ChrisM90/TeensyBoy/Arduino/TeensyBoy/GBA.cpp

/* TeenyBoy code is placed under the MIT license
   Copyright (c) 2017 Chris Mortimer

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
   THE SOFTWARE IS PROVIDED "AS IS", WITHOUT WARRANTY OF ANY KIND,
   EXPRESS OR IMPLIED, INCLUDING BUT NOT LIMITED TO THE WARRANTIES OF
   MERCHANTABILITY, FITNESS FOR A PARTICULAR PURPOSE AND
   NONINFRINGEMENT. IN NO EVENT SHALL THE AUTHORS OR COPYRIGHT HOLDERS
   BE LIABLE FOR ANY CLAIM, DAMAGES OR OTHER LIABILITY, WHETHER IN AN
   ACTION OF CONTRACT, TORT OR OTHERWISE, ARISING FROM, OUT OF OR IN
   CONNECTION WITH THE SOFTWARE OR THE USE OR OTHER DEALINGS IN THE
   SOFTWARE.
*/

#include "GBA.h"

#define SCREEN_WIDTH  ILI9341_TFTWIDTH
#define SCREEN_HEIGHT ILI9341_TFTHEIGHT
#define TFT_DC      15
#define TFT_CS      10
#define TFT_RST     27
#define TFT_MOSI    11
#define TFT_SCLK    13
#define TFT_MISO    12

#define WIN0H 0x40
#define WIN1H 0x42
#define WIN0V 0x44
#define WIN1V 0x46
#define WININ 0x48
#define WINOUT 0x4A

#define BG0CNT 0x8
#define BG1CNT 0xA
#define BG2CNT 0xC
#define BG3CNT 0xE

#define BG2X_L 0x28
#define BG2X_H 0x2A
#define BG2Y_L 0x2C
#define BG2Y_H 0x2E

#define BG3X_L 0x38
#define BG3X_H 0x3A
#define BG3Y_L 0x3C
#define BG3Y_H 0x3E

#define DISPCNT 0x0
#define DISPSTAT 0x4

#define ioRegStart  0x00048000 //0x48000 - 0x484FF = 0x4FF
#define vRamStart   0x00048500 //0x48500 - 0x684FF = 0x1FFFF
#define palRamStart 0x00068500 //0x68500 - 0x688FF = 0x3FF
#define OAM_BASE 0x7000000

#define ButtonA 18
#define ButtonB 17
#define ButtonSelect 26
#define ButtonStart 16
#define ButtonLeft 20
#define ButtonRight 19
#define ButtonUp 22
#define ButtonDown 21
#define ButtonRSholder 38
#define ButtonLSholder 39

int32_t vramCycles = 0;
bool inHblank = false;
uint16_t curLine = 0;

// Window helper variables
uint8_t win0x1, win0x2, win0y1, win0y2;
uint8_t win1x1, win1x2, win1y1, win1y2;
uint8_t win0Enabled, win1Enabled, winObjEnabled, winOutEnabled;
bool winEnabled;

uint8_t blendSource, blendTarget;
uint8_t blendA, blendB, blendY;
int32_t blendType;
uint16_t dispCnt;

uint8_t windowCover[240];
uint8_t Blend[240];

unsigned long FrameTime = 0;

Processor *processor;

void GBA::Initilise(class File *rom)
{  
  ILI9341_t3DMA screen = ILI9341_t3DMA(TFT_CS, TFT_DC, TFT_RST, TFT_MOSI, TFT_SCLK, TFT_MISO);
  tft = &screen;
  tft->begin();
  tft->dfillScreen(ILI9341_BLACK);
  tft->refreshOnce();

  pinMode(ButtonA, INPUT_PULLUP);
  pinMode(ButtonB, INPUT_PULLUP);
  pinMode(ButtonSelect, INPUT_PULLUP);
  pinMode(ButtonStart, INPUT_PULLUP);
  pinMode(ButtonLeft, INPUT_PULLUP);
  pinMode(ButtonRight, INPUT_PULLUP);
  pinMode(ButtonUp, INPUT_PULLUP);
  pinMode(ButtonDown, INPUT_PULLUP);
  pinMode(ButtonRSholder, INPUT_PULLUP);
  pinMode(ButtonLSholder, INPUT_PULLUP);

  Processor GBAProcessor;
  processor = &GBAProcessor;
  processor->CreateCores(processor, rom, false);
}

void GBA::Update()
{
  const int32_t numSteps = 2284;
  const int32_t cycleStep = 123;
  
  for (int32_t i = 0; i < numSteps; i++)
  {
    GetButtons();
    
    if (vramCycles <= 0)
    {
      if (inHblank)
      {
        vramCycles += 960;
        LeaveHBlank();
        inHblank = false;
      }
      else
      {
        vramCycles += 272;
        RenderLine();
        EnterHBlank();
        inHblank = true;
      }
    }

    processor->Execute(cycleStep);

    vramCycles -= cycleStep;

    processor->FireIrq();
  }
}

void GBA::EnterVBlank()
{
  uint16_t dispstat = processor->ReadU16(DISPSTAT, ioRegStart); //Read DISPSTAT 0x4 from IOReg
  dispstat |= 1;
  processor->WriteU16(DISPSTAT, ioRegStart, dispstat);//Write new DISPSTAT 0x4 to IOReg

  // Render the frame

  if(FrameTime != 0)
  {
    FPS = 1000000.0f / (float)(micros() - FrameTime);
  }

  Serial.println("FPS: " + String(FPS));
  tft->refreshOnce();
  FrameTime = micros();
  
  if ((dispstat & (1 << 3)) != 0)
  {
    // Fire the vblank irq
    processor->RequestIrq(0);
  }

  // Check for DMA triggers
  processor->VBlankDma();
}

void GBA::LeaveVBlank()
{
  uint16_t dispstat = processor->ReadU16(DISPSTAT, ioRegStart); //Read DISPSTAT 0x4 from IOReg
  dispstat &= 0xFFFE;
  processor->WriteU16(DISPSTAT, ioRegStart, dispstat);//Write new DISPSTAT 0x4 to IOReg

  processor->UpdateKeyState();

  // Update the rot/scale values
  processor->bgx[0] = (int32_t)processor->ReadU32(BG2X_L, ioRegStart); //Read BG2X_L from IOReg
  processor->bgx[1] = (int32_t)processor->ReadU32(BG3X_L, ioRegStart); //Read BG3X_L from IOReg
  processor->bgy[0] = (int32_t)processor->ReadU32(BG2Y_L, ioRegStart); //Read BG2Y_L from IOReg
  processor->bgy[1] = (int32_t)processor->ReadU32(BG3Y_L, ioRegStart); //Read BG3Y_L from IOReg
}

void GBA::EnterHBlank()
{
  uint16_t dispstat = processor->ReadU16(DISPSTAT, ioRegStart); //Read DISPSTAT 0x4 from IOReg
  dispstat |= 1 << 1;
  processor->WriteU16(DISPSTAT, ioRegStart, dispstat);//Write new DISPSTAT 0x4 to IOReg

  // Advance the bgx registers
  for (int32_t bg = 0; bg <= 1; bg++)
  {
    int16_t dmx = (int16_t)processor->ReadU16(BG2PB + (uint32_t)bg * 0x10, ioRegStart); //Read BG2PB from IOReg
    int16_t dmy = (int16_t)processor->ReadU16(BG2PD+ (uint32_t)bg * 0x10, ioRegStart); //Read BG2PD from IOReg
    processor->bgx[bg] += dmx;
    processor->bgy[bg] += dmy;
  }

  if (curLine < 160)
  {
    processor->HBlankDma();

    // Trigger hblank irq
    if ((dispstat & (1 << 4)) != 0)
    {
      processor->RequestIrq(1);
    }
  }
}

void GBA::LeaveHBlank()
{
  uint16_t dispstat = processor->ReadU16(DISPSTAT, ioRegStart); //Read DISPSTAT 0x4 from IOReg
  dispstat &= 0xFFF9;
  processor->WriteU16(DISPSTAT, ioRegStart, dispstat);//Write new DISPSTAT 0x4 to IOReg

  // Move to the next line
  curLine++;

  if (curLine >= 228)
  {
    // Start again at the beginning
    curLine = 0;
  }

  // Update registers
  processor->WriteU16(VCOUNT, ioRegStart, (uint16_t)curLine); //Write VCOUNT 0x6 in IOReg

  // Check for vblank
  if (curLine == 160)
  {
    EnterVBlank();
  }
  else if (curLine == 0)
  {
    LeaveVBlank();
  }

  // Check y-line trigger
  if (((dispstat >> 8) & 0xff) == curLine)
  {
    dispstat = (uint16_t)(processor->ReadU16(DISPSTAT, ioRegStart) | (1 << 2)); //Read DISPSTAT 0x4 from IOReg
    processor->WriteU16(DISPSTAT, ioRegStart, dispstat);//Write new DISPSTAT 0x4 to IOReg

    if ((dispstat & (1 << 5)) != 0)
    {
      processor->RequestIrq(2);
    }
  }
}

void GBA::GetButtons()
{
  //Button Index
  // 0 = A
  // 1 = B
  // 2 = Select
  // 3 = Start
  // 4 = Right
  // 5 = Left
  // 6 = Up
  // 7 = Down
  // 8 = Right Sholder
  // 9 = Left Sholder
  
  uint16_t keyreg = 0x3FF;

  if(!digitalReadFast(ButtonA))
  {
    keyreg &= (uint16_t)(~(1U << 0)); //Pressed
  }
  else
  {
    keyreg |= (uint16_t)(1U << 0); //Unpressed
  }

  if(!digitalReadFast(ButtonB))
  {
    keyreg &= (uint16_t)(~(1U << 1)); //Pressed
  }
  else
  {
    keyreg |= (uint16_t)(1U << 1); //Unpressed
  }

  if(!digitalReadFast(ButtonSelect))
  {
    keyreg &= (uint16_t)(~(1U << 2)); //Pressed
  }
  else
  {
    keyreg |= (uint16_t)(1U << 2); //Unpressed
  }

  if(!digitalReadFast(ButtonStart))
  {
    keyreg &= (uint16_t)(~(1U << 3)); //Pressed
  }
  else
  {
    keyreg |= (uint16_t)(1U << 3); //Unpressed
  }

  if(!digitalReadFast(ButtonLeft))
  {
    keyreg &= (uint16_t)(~(1U << 4)); //Pressed
  }
  else
  {
    keyreg |= (uint16_t)(1U << 4); //Unpressed
  }

  if(!digitalReadFast(ButtonRight))
  {
    keyreg &= (uint16_t)(~(1U << 5)); //Pressed
  }
  else
  {
    keyreg |= (uint16_t)(1U << 5); //Unpressed
  }
  
  if(!digitalReadFast(ButtonUp))
  {
    keyreg &= (uint16_t)(~(1U << 6)); //Pressed
  }
  else
  {
    keyreg |= (uint16_t)(1U << 6); //Unpressed
  }

  if(!digitalReadFast(ButtonDown))
  {
    keyreg &= (uint16_t)(~(1U << 7)); //Pressed
  }
  else
  {
    keyreg |= (uint16_t)(1U << 7); //Unpressed
  }

  if(!digitalReadFast(ButtonRSholder))
  {
    keyreg &= (uint16_t)(~(1U << 8)); //Pressed
  }
  else
  {
    keyreg |= (uint16_t)(1U << 8); //Unpressed
  }

  if(!digitalReadFast(ButtonLSholder))
  {
    keyreg &= (uint16_t)(~(1U << 9)); //Pressed
  }
  else
  {
    keyreg |= (uint16_t)(1U << 9); //Unpressed
  }

  processor->keyState = keyreg;
}

void GBA::RenderLine()
{
  if(curLine >= 160)
  {
    return;
  }

  dispCnt = processor->ReadU16(DISPCNT, ioRegStart); //Read DISPCNT 0x0 from IOReg

  if ((dispCnt & (1 << 7)) != 0)
  {
    uint16_t bgColor = GBAToColor(0x7FFF); //White
    for (int32_t i = 0; i < 240; i++) 
    {
      DrawPixel(curLine, i, bgColor);
    }
  }
  else
  {
    winEnabled = false;

    if ((dispCnt & (1 << 13)) != 0)
    {
      // Calculate window 0 information
      uint16_t winy = processor->ReadU16(WIN0V, ioRegStart); //Read WIN0V 0x0 from IOReg
      win0y1 = (uint8_t)(winy >> 8);
      win0y2 = (uint8_t)(winy & 0xff);
      uint16_t winx = processor->ReadU16(WIN0H, ioRegStart); //Read WIN0H 0x0 from IOReg
      win0x1 = (uint8_t)(winx >> 8);
      win0x2 = (uint8_t)(winx & 0xff);

      if (win0x2 > 240 || win0x1 > win0x2)
      {
        win0x2 = 240;
      }

      if (win0y2 > 160 || win0y1 > win0y2)
      {
        win0y2 = 160;
      }

      win0Enabled = processor->ReadU8(WININ, ioRegStart);
      winEnabled = true;
    }

    if ((dispCnt & (1 << 14)) != 0)
    {
      // Calculate window 1 information
      uint16_t winy = processor->ReadU16(WIN1V, ioRegStart); //Read WIN1V 0x0 from IOReg
      win1y1 = (uint8_t)(winy >> 8);
      win1y2 = (uint8_t)(winy & 0xff);
      uint16_t winx = processor->ReadU16(WIN1H, ioRegStart); //Read WIN1H 0x0 from IOReg
      win1x1 = (uint8_t)(winx >> 8);
      win1x2 = (uint8_t)(winx & 0xff);

      if (win1x2 > 240 || win1x1 > win1x2)
      {
        win1x2 = 240;
      }

      if (win1y2 > 160 || win1y1 > win1y2)
      {
        win1y2 = 160;
      }

      win1Enabled = processor->ReadU8(WININ + 1, ioRegStart);
      winEnabled = true;
    }

    if ((dispCnt & (1 << 15)) != 0 && (dispCnt & (1 << 12)) != 0)
    {
      // Object windows are enabled
      winObjEnabled = processor->ReadU8(WINOUT + 1, ioRegStart);
      winEnabled = true;
    }

    if (winEnabled)
    {
      winOutEnabled = processor->ReadU8(WINOUT, ioRegStart);
    }

    // Calculate blending information
    uint16_t bldcnt = processor->ReadU16(BLDCNT, ioRegStart); //Read BLD 0x0 from IOReg
    blendType = (bldcnt >> 6) & 0x3;
    blendSource = (uint8_t)(bldcnt & 0x3F);
    blendTarget = (uint8_t)((bldcnt >> 8) & 0x3F);

    uint16_t bldalpha = processor->ReadU16(BLDALPHA, ioRegStart); //Read BLDALPHA 0x0 from IOReg
    blendA = (uint8_t)(bldalpha & 0x1F);
    if (blendA > 0x10) blendA = 0x10;
    blendB = (uint8_t)((bldalpha >> 8) & 0x1F);
    if (blendB > 0x10) blendB = 0x10;

    blendY = (uint8_t)(processor->ReadU8(BLDY, ioRegStart) & 0x1F);
    if (blendY > 0x10) blendY = 0x10;

    switch (dispCnt & 0x7)
    {
      case 0: RenderMode0Line(); break;
      case 1: RenderMode1Line(); break;
      case 2: RenderMode2Line(); break;
      case 3: RenderMode3Line(); break;
      case 4: RenderMode4Line(); break;
      case 5: RenderMode5Line(); break;
    }
  }
}

void GBA::DrawBackdrop()
{
  // Initialize window coverage buffer if neccesary
  if (winEnabled)
  {
    for (int32_t i = 0; i < 240; i++)
    {
      windowCover[i] = winOutEnabled;
    }

    if ((dispCnt & (1 << 15)) != 0)
    {
      // Sprite window
      DrawSpriteWindows();
    }

    if ((dispCnt & (1 << 14)) != 0)
    {
      // Window 1
      if (curLine >= win1y1 && curLine < win1y2)
      {
        for (int32_t i = win1x1; i < win1x2; i++)
        {
          windowCover[i] = win1Enabled;
        }
      }
    }

    if ((dispCnt & (1 << 13)) != 0)
    {
      // Window 0
      if (curLine >= win0y1 && curLine < win0y2)
      {
        for (int32_t i = win0x1; i < win0x2; i++)
        {
          windowCover[i] = win0Enabled;
        }
      }
    }
  }

  // Draw backdrop first
  uint16_t bgColor = processor->ReadU16(0, palRamStart);
  uint16_t modColor = bgColor;

  if (blendType == 2 && (blendSource & (1 << 5)) != 0)
  {
    // Brightness increase
    uint8_t r = (uint8_t)((bgColor) & 0x1F);       //First 5 Bits
    uint8_t g = (uint8_t)((bgColor >> 5) & 0x1F);  //Middle 5 Bits
    uint8_t b = (uint8_t)(bgColor >> 10) & 0x1F;   //Last 5 Bits
    
    r = r + (((0xFF - r) * blendY) >> 4);
    g = g + (((0xFF - g) * blendY) >> 4);
    b = b + (((0xFF - b) * blendY) >> 4);
    modColor = (b << 0) | (g << 5) | (r << 11);
  }
  else if (blendType == 3 && (blendSource & (1 << 5)) != 0)
  {
    // Brightness decrease
    uint8_t r = (uint8_t)((bgColor) & 0x1F);       //First 5 Bits
    uint8_t g = (uint8_t)((bgColor >> 5) & 0x1F);  //Middle 5 Bits
    uint8_t b = (uint8_t)(bgColor >> 10) & 0x1F;   //Last 5 Bits
    
    r = r - ((r * blendY) >> 4);
    g = g - ((g * blendY) >> 4);
    b = b - ((b * blendY) >> 4);
    
    modColor = (b << 0) | (g << 5) | (r << 11);
  }

  if (winEnabled)
  {
    for (int32_t i = 0; i < 240; i++)
    {
      if ((windowCover[i] & (1 << 5)) != 0)
      {
        DrawPixel(curLine, i, modColor);
      }
      else
      {
        DrawPixel(curLine, i, bgColor);
      }
      Blend[i] = 1 << 5;
    }
  }
  else
  {
    for (int32_t i = 0; i < 240; i++)
    {
      DrawPixel(curLine, i, modColor);
      Blend[i] = 1 << 5;
    }
  }
}

void GBA::RenderTextBg(uint8_t bg)
{
  if (winEnabled)
  {
    switch (blendType)
    {
    case 0:
      RenderTextBgWindow(bg);
      break;
    case 1:
      if ((blendSource & (1 << bg)) != 0)
        RenderTextBgWindowBlend(bg);
      else
        RenderTextBgWindow(bg);
      break;
    case 2:
      if ((blendSource & (1 << bg)) != 0)
        RenderTextBgWindowBrightInc(bg);
      else
        RenderTextBgWindow(bg);
      break;
    case 3:
      if ((blendSource & (1 << bg)) != 0)
        RenderTextBgWindowBrightDec(bg);
      else
        RenderTextBgWindow(bg);
      break;
    }
  }
  else
  {
    switch (blendType)
    {
    case 0:
      RenderTextBgNormal(bg);
      break;
    case 1:
      if ((blendSource & (1 << bg)) != 0)
        RenderTextBgBlend(bg);
      else
        RenderTextBgNormal(bg);
      break;
    case 2:
      if ((blendSource & (1 << bg)) != 0)
        RenderTextBgBrightInc(bg);
      else
        RenderTextBgNormal(bg);
      break;
    case 3:
      if ((blendSource & (1 << bg)) != 0)
        RenderTextBgBrightDec(bg);
      else
        RenderTextBgNormal(bg);
      break;
    }
  }
}

void GBA::DrawSprites(uint8_t pri)
{ 
  if (winEnabled)
  {
    switch (blendType)
    {
    case 0:
      DrawSpritesWindow(pri);
      break;
    case 1:
      if ((blendSource & (1 << 4)) != 0)
        DrawSpritesWindowBlend(pri);
      else
        DrawSpritesWindow(pri);
      break;
    case 2:
      if ((blendSource & (1 << 4)) != 0)
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
        {
          RenderRotScaleBg(i);
        }
      }
    }

    DrawSprites(pri);
  }
}

void GBA::RenderMode3Line()
{
  uint16_t bg2Cnt = processor->ReadU16(BG2CNT, ioRegStart); //Read BG0CNT 0x0 from IOReg

  DrawBackdrop();

  uint8_t blendMaskType = (uint8_t)(1 << 2);

  int32_t bgPri = bg2Cnt & 0x3;
  for (int32_t pri = 3; pri > bgPri; pri--)
  {
    DrawSprites(pri);
  }

  if ((dispCnt & (1 << 10)) != 0)
  {
    // Background enabled, render it
    uint32_t x = processor->bgx[0];
    uint32_t y = processor->bgy[0];

    int16_t dx = (int16_t)processor->ReadU16(BG2PA, ioRegStart);
    int16_t dy = (int16_t)processor->ReadU16(BG2PC, ioRegStart);

    for (int32_t i = 0; i < 240; i++)
    {
      int32_t ax = ((int32_t)x) >> 8;
      int32_t ay = ((int32_t)y) >> 8;

      if (ax >= 0 && ax < 240 && ay >= 0 && ay < 160)
      {
        int32_t curIdx = ((ay * 240) + ax) * 2;
        
        DrawPixel(curLine, i, GBAToColor(processor->ReadU16(curIdx, vRamStart))); //Read From VRAM
        Blend[i] = blendMaskType;
      }
      x += dx;
      y += dy;
    }
  }

  for (int32_t pri = bgPri; pri >= 0; pri--)
  {
    DrawSprites(pri);
  }
}

void GBA::RenderMode4Line()
{
  uint16_t bg2Cnt = processor->ReadU16(BG2CNT, ioRegStart); //Read BG0CNT 0x0 from IOReg
  
  DrawBackdrop();

  uint8_t blendMaskType = (uint8_t)(1 << 2);

  int32_t bgPri = bg2Cnt & 0x3;
  
  for (int32_t pri = 3; pri > bgPri; pri--)
  {
    DrawSprites(pri);
  }

  if ((dispCnt & (1 << 10)) != 0)
  {
    // Background enabled, render it
    int32_t baseIdx = 0;
    if ((dispCnt & (1 << 4)) == 1 << 4) baseIdx = 0xA000;

    int32_t x = processor->bgx[0];
    int32_t y = processor->bgy[0];

    int16_t dx = (int16_t)processor->ReadU16(BG2PA, ioRegStart);
    int16_t dy = (int16_t)processor->ReadU16(BG2PC, ioRegStart);

    for (int32_t i = 0; i < 240; i++)
    {
      int32_t ax = ((int32_t)x) >> 8;
      int32_t ay = ((int32_t)y) >> 8;

      if (ax >= 0 && ax < 240 && ay >= 0 && ay < 160)
      {
        int32_t lookup = processor->ReadU8(baseIdx + (ay * 240) + ax, vRamStart); //VRAM Lookup
        
        if (lookup != 0)
        {                       
          DrawPixel(curLine, i, GBAToColor(processor->ReadU16(lookup * 2, palRamStart))); //Palette Lookup
          Blend[i] = blendMaskType;
        }
      }
      x += dx;
      y += dy;
    }
  }

  for (int32_t pri = bgPri; pri >= 0; pri--)
  {
    DrawSprites(pri);
  }
}

void GBA::RenderMode5Line()
{
  uint16_t bg2Cnt = processor->ReadU16(BG2CNT, ioRegStart); //Read BG0CNT 0x0 from IOReg

  DrawBackdrop();

  uint8_t blendMaskType = (uint8_t)(1 << 2);

  int32_t bgPri = bg2Cnt & 0x3;
  for (int32_t pri = 3; pri > bgPri; pri--)
  {
    DrawSprites(pri);
  }

  if ((dispCnt & (1 << 10)) != 0)
  {
    // Background enabled, render it
    int32_t baseIdx = 0;
    if ((dispCnt & (1 << 4)) == 1 << 4) baseIdx += 160 * 128 * 2;

    int32_t x = processor->bgx[0];
    int32_t y = processor->bgy[0];

    int16_t dx = (int16_t)processor->ReadU16(BG2PA, ioRegStart);
    int16_t dy = (int16_t)processor->ReadU16(BG2PC, ioRegStart);

    for (int32_t i = 0; i < 240; i++)
    {
      int32_t ax = ((int32_t)x) >> 8;
      int32_t ay = ((int32_t)y) >> 8;

      if (ax >= 0 && ax < 160 && ay >= 0 && ay < 128)
      {
        int32_t curIdx = (int32_t)(ay * 160 + ax) * 2;

        DrawPixel(curLine, i, GBAToColor(processor->ReadU16(baseIdx + curIdx, vRamStart)));
        Blend[i] = blendMaskType;
      }
      x += dx;
      y += dy;
    }
  }

  for (int32_t pri = bgPri; pri >= 0; pri--)
  {
    DrawSprites(pri);
  }
}

void GBA::DrawSpriteWindows()
{
  // OBJ must be enabled in this.dispCnt
  if ((dispCnt & (1 << 12)) == 0) return;

  for (int32_t oamNum = 127; oamNum >= 0; oamNum--)
  {
    uint16_t attr0 = processor->ReadU16Debug(OAM_BASE + (uint32_t)(oamNum * 8) + 0);

    // Not an object window, so continue
    if (((attr0 >> 10) & 3) != 2) continue;

    uint16_t attr1 = processor->ReadU16Debug(OAM_BASE + (uint32_t)(oamNum * 8) + 2);
    uint16_t attr2 = processor->ReadU16Debug(OAM_BASE + (uint32_t)(oamNum * 8) + 4);

    int32_t x = attr1 & 0x1FF;
    int32_t y = attr0 & 0xFF;

    int32_t Width = -1, Height = -1;
    switch ((attr0 >> 14) & 3)
    {
    case 0:
      // Square
      switch ((attr1 >> 14) & 3)
      {
      case 0: Width = 8; Height = 8; break;
      case 1: Width = 16; Height = 16; break;
      case 2: Width = 32; Height = 32; break;
      case 3: Width = 64; Height = 64; break;
      }
      break;
    case 1:
      // Horizontal Rectangle
      switch ((attr1 >> 14) & 3)
      {
      case 0: Width = 16; Height = 8; break;
      case 1: Width = 32; Height = 8; break;
      case 2: Width = 32; Height = 16; break;
      case 3: Width = 64; Height = 32; break;
      }
      break;
    case 2:
      // Vertical Rectangle
      switch ((attr1 >> 14) & 3)
      {
      case 0: Width = 8; Height = 16; break;
      case 1: Width = 8; Height = 32; break;
      case 2: Width = 16; Height = 32; break;
      case 3: Width = 32; Height = 64; break;
      }
      break;
    }

    // Check double size flag here

    int32_t rWidth = Width, rHeight = Height;
    if ((attr0 & (1 << 8)) != 0)
    {
      // Rot-scale on
      if ((attr0 & (1 << 9)) != 0)
      {
        rWidth *= 2;
        rHeight *= 2;
      }
    }
    else
    {
      // Invalid sprite
      if ((attr0 & (1 << 9)) != 0)
        Width = -1;
    }

    if (Width == -1)
    {
      // Invalid sprite
      continue;
    }

    // Y clipping
    if (y > ((y + rHeight) & 0xff))
    {
      if (curLine >= ((y + rHeight) & 0xff) && !(y < curLine)) continue;
    }
    else
    {
      if (curLine < y || curLine >= ((y + rHeight) & 0xff)) continue;
    }

    int32_t scale = 1;
    if ((attr0 & (1 << 13)) != 0) scale = 2;

    int32_t spritey = curLine - y;
    if (spritey < 0) spritey += 256;

    if ((attr0 & (1 << 8)) == 0)
    {
      if ((attr1 & (1 << 13)) != 0) spritey = (Height - 1) - spritey;

      int32_t baseSprite;
      if ((dispCnt & (1 << 6)) != 0)
      {
        // 1 dimensional
        baseSprite = (attr2 & 0x3FF) + ((spritey / 8) * (Width / 8)) * scale;
      }
      else
      {
        // 2 dimensional
        baseSprite = (attr2 & 0x3FF) + ((spritey / 8) * 0x20);
      }

      int32_t baseInc = scale;
      if ((attr1 & (1 << 12)) != 0)
      {
        baseSprite += ((Width / 8) * scale) - scale;
        baseInc = -baseInc;
      }

      if ((attr0 & (1 << 13)) != 0)
      {
        // 256 colors
        for (int32_t i = x; i < x + Width; i++)
        {
          if ((i & 0x1ff) < 240)
          {
            int32_t tx = (i - x) & 7;
            if ((attr1 & (1 << 12)) != 0) tx = 7 - tx;
            int32_t curIdx = baseSprite * 32 + ((spritey & 7) * 8) + tx;
            int32_t lookup = processor->ReadU8(0x10000 + curIdx, vRamStart);
            if (lookup != 0)
            {
              windowCover[i & 0x1ff] = winObjEnabled;
            }
          }
          if (((i - x) & 7) == 7) baseSprite += baseInc;
        }
      }
      else
      {
        // 16 colors
        for (int32_t i = x; i < x + Width; i++)
        {
          if ((i & 0x1ff) < 240)
          {
            int32_t tx = (i - x) & 7;
            if ((attr1 & (1 << 12)) != 0) tx = 7 - tx;
            int32_t curIdx = baseSprite * 32 + ((spritey & 7) * 4) + (tx / 2);
            int32_t lookup = processor->ReadU8(0x10000 + curIdx, vRamStart);
            if ((tx & 1) == 0)
            {
              lookup &= 0xf;
            }
            else
            {
              lookup >>= 4;
            }
            if (lookup != 0)
            {
              windowCover[i & 0x1ff] = winObjEnabled;
            }
          }
          if (((i - x) & 7) == 7) baseSprite += baseInc;
        }
      }
    }
    else
    {
      int32_t rotScaleParam = (attr1 >> 9) & 0x1F;

      int16_t dx = (int16_t)processor->ReadU16Debug(OAM_BASE + (uint32_t)(rotScaleParam * 8 * 4) + 0x6);
      int16_t dmx = (int16_t)processor->ReadU16Debug(OAM_BASE + (uint32_t)(rotScaleParam * 8 * 4) + 0xE);
      int16_t dy = (int16_t)processor->ReadU16Debug(OAM_BASE + (uint32_t)(rotScaleParam * 8 * 4) + 0x16);
      int16_t dmy = (int16_t)processor->ReadU16Debug(OAM_BASE + (uint32_t)(rotScaleParam * 8 * 4) + 0x1E);

      int32_t cx = rWidth / 2;
      int32_t cy = rHeight / 2;

      int32_t baseSprite = attr2 & 0x3FF;
      int32_t pitch;

      if ((dispCnt & (1 << 6)) != 0)
      {
        // 1 dimensional
        pitch = (Width / 8) * scale;
      }
      else
      {
        // 2 dimensional
        pitch = 0x20;
      }

      int16_t rx = (int16_t)((dmx * (spritey - cy)) - (cx * dx) + (Width << 7));
      int16_t ry = (int16_t)((dmy * (spritey - cy)) - (cx * dy) + (Height << 7));

      // Draw a rot/scale sprite
      if ((attr0 & (1 << 13)) != 0)
      {
        // 256 colors
        for (int32_t i = x; i < x + rWidth; i++)
        {
          int32_t tx = rx >> 8;
          int32_t ty = ry >> 8;

          if ((i & 0x1ff) < 240 && tx >= 0 && tx < Width && ty >= 0 && ty < Height)
          {
            int32_t curIdx = (baseSprite + ((ty / 8) * pitch) + ((tx / 8) * scale)) * 32 + ((ty & 7) * 8) + (tx & 7);
            int32_t lookup = processor->ReadU8(0x10000 + curIdx, vRamStart);
            if (lookup != 0)
            {
              windowCover[i & 0x1ff] = winObjEnabled;
            }
          }

          rx += dx;
          ry += dy;
        }
      }
      else
      {
        // 16 colors
        for (int32_t i = x; i < x + rWidth; i++)
        {
          int32_t tx = rx >> 8;
          int32_t ty = ry >> 8;

          if ((i & 0x1ff) < 240 && tx >= 0 && tx < Width && ty >= 0 && ty < Height)
          {
            int32_t curIdx = (baseSprite + ((ty / 8) * pitch) + ((tx / 8) * scale)) * 32 + ((ty & 7) * 4) + ((tx & 7) / 2);
            int32_t lookup = processor->ReadU8(0x10000 + curIdx, vRamStart);
            if ((tx & 1) == 0)
            {
              lookup &= 0xf;
            }
            else
            {
              lookup >>= 4;
            }
            if (lookup != 0)
            {
              windowCover[i & 0x1ff] = winObjEnabled;
            }
          }
          rx += dx;
          ry += dy;
        }
      }
    }
  }
}
//-----------Sprite Drawing--------------------------------
void GBA::DrawSpritesNormal(int8_t priority)
{
  // OBJ must be enabled in this.dispCnt
  if ((dispCnt & (1 << 12)) == 0) return;

  uint8_t blendMaskType = (uint8_t)(1 << 4);

  for (int32_t oamNum = 127; oamNum >= 0; oamNum--)
  {
    uint16_t attr2 = processor->ReadU16Debug(OAM_BASE + (uint32_t)(oamNum * 8) + 4);

    if (((attr2 >> 10) & 3) != priority) continue;

    uint16_t attr0 = processor->ReadU16Debug(OAM_BASE + (uint32_t)(oamNum * 8) + 0);
    uint16_t attr1 = processor->ReadU16Debug(OAM_BASE + (uint32_t)(oamNum * 8) + 2);

    int32_t x = attr1 & 0x1FF;
    int32_t y = attr0 & 0xFF;

    bool semiTransparent = false;

    switch ((attr0 >> 10) & 3)
    {
    case 1:
      // Semi-transparent
      semiTransparent = true;
      break;
    case 2:
      // Obj window
      continue;
    case 3:
      continue;
    }

    if ((dispCnt & 0x7) >= 3 && (attr2 & 0x3FF) < 0x200) continue;

    int32_t Width = -1, Height = -1;
    switch ((attr0 >> 14) & 3)
    {
    case 0:
      // Square
      switch ((attr1 >> 14) & 3)
      {
      case 0: Width = 8; Height = 8; break;
      case 1: Width = 16; Height = 16; break;
      case 2: Width = 32; Height = 32; break;
      case 3: Width = 64; Height = 64; break;
      }
      break;
    case 1:
      // Horizontal Rectangle
      switch ((attr1 >> 14) & 3)
      {
      case 0: Width = 16; Height = 8; break;
      case 1: Width = 32; Height = 8; break;
      case 2: Width = 32; Height = 16; break;
      case 3: Width = 64; Height = 32; break;
      }
      break;
    case 2:
      // Vertical Rectangle
      switch ((attr1 >> 14) & 3)
      {
      case 0: Width = 8; Height = 16; break;
      case 1: Width = 8; Height = 32; break;
      case 2: Width = 16; Height = 32; break;
      case 3: Width = 32; Height = 64; break;
      }
      break;
    }

    // Check double size flag here

    int32_t rWidth = Width, rHeight = Height;
    if ((attr0 & (1 << 8)) != 0)
    {
      // Rot-scale on
      if ((attr0 & (1 << 9)) != 0)
      {
        rWidth *= 2;
        rHeight *= 2;
      }
    }
    else
    {
      // Invalid sprite
      if ((attr0 & (1 << 9)) != 0)
        Width = -1;
    }

    if (Width == -1)
    {
      // Invalid sprite
      continue;
    }

    // Y clipping
    if (y > ((y + rHeight) & 0xff))
    {
      if (curLine >= ((y + rHeight) & 0xff) && !(y < curLine)) continue;
    }
    else
    {
      if (curLine < y || curLine >= ((y + rHeight) & 0xff)) continue;
    }

    int32_t scale = 1;
    if ((attr0 & (1 << 13)) != 0) scale = 2;

    int32_t spritey = curLine - y;
    if (spritey < 0) spritey += 256;

    if (semiTransparent)
    {
      if ((attr0 & (1 << 8)) == 0)
      {
        if ((attr1 & (1 << 13)) != 0) spritey = (Height - 1) - spritey;

        int32_t baseSprite;
        if ((dispCnt & (1 << 6)) != 0)
        {
          // 1 dimensional
          baseSprite = (attr2 & 0x3FF) + ((spritey / 8) * (Width / 8)) * scale;
        }
        else
        {
          // 2 dimensional
          baseSprite = (attr2 & 0x3FF) + ((spritey / 8) * 0x20);
        }

        int32_t baseInc = scale;
        if ((attr1 & (1 << 12)) != 0)
        {
          baseSprite += ((Width / 8) * scale) - scale;
          baseInc = -baseInc;
        }

        if ((attr0 & (1 << 13)) != 0)
        {
          // 256 colors
          for (int32_t i = x; i < x + Width; i++)
          {
            if ((i & 0x1ff) < 240 && true)
            {
              int32_t tx = (i - x) & 7;
              if ((attr1 & (1 << 12)) != 0) tx = 7 - tx;
              int32_t curIdx = baseSprite * 32 + ((spritey & 7) * 8) + tx;
              int32_t lookup = processor->ReadU8(0x10000 + curIdx, vRamStart);
              if (lookup != 0)
              {
                uint16_t pixelColor = processor->ReadU16(0x200 + lookup * 2, palRamStart);
                
                if ((Blend[i & 0x1ff] & blendTarget) != 0 && Blend[i & 0x1ff] != blendMaskType)
                {
                  uint16_t r = (uint8_t)((((pixelColor) & 0x1F) * blendA) >> 4);       //First 5 Bits
                  uint16_t g = (uint8_t)((((pixelColor >> 5) & 0x1F) * blendA) >> 4);  //Middle 5 Bits
                  uint16_t b = (uint8_t)((((pixelColor >> 10) & 0x1F) * blendA) >> 4);   //Last 5 Bits
                  uint16_t sourceValue = tft->dgetPixel(curLine, (i & 0x1ff));
                  r += (uint8_t)((((sourceValue >> 11) & 0x1F) * blendB) >> 4); //R
                  g += (uint8_t)((((sourceValue >> 5) & 0x3F) * blendB) >> 4); //G
                  b += (uint8_t)((((sourceValue) & 0x1F) * blendB) >> 4); //B
                  if (r > 0xff) r = 0xff;
                  if (g > 0xff) g = 0xff;
                  if (b > 0xff) b = 0xff;
                  pixelColor = ((uint8_t)(b) << 0) | ((uint8_t)(g) << 5) | ((uint8_t)(r) << 11);
                }
                else
                {
                  pixelColor = GBAToColor(pixelColor);
                }
                
                DrawPixel(curLine, (i & 0x1ff), pixelColor); 
                Blend[(i & 0x1ff)] = blendMaskType;
              }
            }
            if (((i - x) & 7) == 7) baseSprite += baseInc;
          }
        }
        else
        {
          // 16 colors
          int32_t palIdx = 0x200 + (((attr2 >> 12) & 0xF) * 16 * 2);
          for (int32_t i = x; i < x + Width; i++)
          {
            if ((i & 0x1ff) < 240 && true)
            {
              int32_t tx = (i - x) & 7;
              if ((attr1 & (1 << 12)) != 0) tx = 7 - tx;
              int32_t curIdx = baseSprite * 32 + ((spritey & 7) * 4) + (tx / 2);
              int32_t lookup = processor->ReadU8(0x10000 + curIdx, vRamStart);
              if ((tx & 1) == 0)
              {
                lookup &= 0xf;
              }
              else
              {
                lookup >>= 4;
              }
              if (lookup != 0)
              {
                uint16_t pixelColor = processor->ReadU16(palIdx + lookup * 2, palRamStart);
                
                if ((Blend[i & 0x1ff] & blendTarget) != 0 && Blend[i & 0x1ff] != blendMaskType)
                {
                  uint16_t r = (uint8_t)((((pixelColor) & 0x1F) * blendA) >> 4);       //First 5 Bits
                  uint16_t g = (uint8_t)((((pixelColor >> 5) & 0x1F) * blendA) >> 4);  //Middle 5 Bits
                  uint16_t b = (uint8_t)((((pixelColor >> 10) & 0x1F) * blendA) >> 4);   //Last 5 Bits
                  uint16_t sourceValue = tft->dgetPixel(curLine, (i & 0x1ff));
                  r += (uint8_t)((((sourceValue >> 11) & 0x1F) * blendB) >> 4); //R
                  g += (uint8_t)((((sourceValue >> 5) & 0x3F) * blendB) >> 4); //G
                  b += (uint8_t)((((sourceValue) & 0x1F) * blendB) >> 4); //B
                  if (r > 0xff) r = 0xff;
                  if (g > 0xff) g = 0xff;
                  if (b > 0xff) b = 0xff;
                  pixelColor = ((uint8_t)(b) << 0) | ((uint8_t)(g) << 5) | ((uint8_t)(r) << 11);
                }
                else
                {
                  pixelColor = GBAToColor(pixelColor);
                }
                
                DrawPixel(curLine, (i & 0x1ff), pixelColor); 
                Blend[(i & 0x1ff)] = blendMaskType;
              }
            }
            if (((i - x) & 7) == 7) baseSprite += baseInc;
          }
        }
      }
      else
      {
        int32_t rotScaleParam = (attr1 >> 9) & 0x1F;

        int16_t dx = (int16_t)processor->ReadU16Debug(OAM_BASE + (uint32_t)(rotScaleParam * 8 * 4) + 0x6);
        int16_t dmx = (int16_t)processor->ReadU16Debug(OAM_BASE + (uint32_t)(rotScaleParam * 8 * 4) + 0xE);
        int16_t dy = (int16_t)processor->ReadU16Debug(OAM_BASE + (uint32_t)(rotScaleParam * 8 * 4) + 0x16);
        int16_t dmy = (int16_t)processor->ReadU16Debug(OAM_BASE + (uint32_t)(rotScaleParam * 8 * 4) + 0x1E);

        int32_t cx = rWidth / 2;
        int32_t cy = rHeight / 2;

        int32_t baseSprite = attr2 & 0x3FF;
        int32_t pitch;

        if ((dispCnt & (1 << 6)) != 0)
        {
          // 1 dimensional
          pitch = (Width / 8) * scale;
        }
        else
        {
          // 2 dimensional
          pitch = 0x20;
        }

        int32_t rx = (int32_t)((dmx * (spritey - cy)) - (cx * dx) + (Width << 7));
        int32_t ry = (int32_t)((dmy * (spritey - cy)) - (cx * dy) + (Height << 7));

        // Draw a rot/scale sprite
        if ((attr0 & (1 << 13)) != 0)
        {
          // 256 colors
          for (int32_t i = x; i < x + rWidth; i++)
          {
            int32_t tx = rx >> 8;
            int32_t ty = ry >> 8;

            if ((i & 0x1ff) < 240 && tx >= 0 && tx < Width && ty >= 0 && ty < Height && true)
            {
              int32_t curIdx = (baseSprite + ((ty / 8) * pitch) + ((tx / 8) * scale)) * 32 + ((ty & 7) * 8) + (tx & 7);
              int32_t lookup = processor->ReadU8(0x10000 + curIdx, vRamStart);
              if (lookup != 0)
              {
                uint16_t pixelColor = processor->ReadU16(0x200 + lookup * 2, palRamStart);
                
                if ((Blend[i & 0x1ff] & blendTarget) != 0 && Blend[i & 0x1ff] != blendMaskType)
                {
                  uint16_t r = (uint8_t)((((pixelColor) & 0x1F) * blendA) >> 4);       //First 5 Bits
                  uint16_t g = (uint8_t)((((pixelColor >> 5) & 0x1F) * blendA) >> 4);  //Middle 5 Bits
                  uint16_t b = (uint8_t)((((pixelColor >> 10) & 0x1F) * blendA) >> 4);   //Last 5 Bits
                  uint16_t sourceValue = tft->dgetPixel(curLine, (i & 0x1ff));
                  r += (uint8_t)((((sourceValue >> 11) & 0x1F) * blendB) >> 4); //R
                  g += (uint8_t)((((sourceValue >> 5) & 0x3F) * blendB) >> 4); //G
                  b += (uint8_t)((((sourceValue) & 0x1F) * blendB) >> 4); //B
                  if (r > 0xff) r = 0xff;
                  if (g > 0xff) g = 0xff;
                  if (b > 0xff) b = 0xff;
                  pixelColor = ((uint8_t)(b) << 0) | ((uint8_t)(g) << 5) | ((uint8_t)(r) << 11);
                }
                else
                {
                  pixelColor = GBAToColor(pixelColor);
                }
                
                DrawPixel(curLine, (i & 0x1ff), pixelColor); 
                Blend[(i & 0x1ff)] = blendMaskType;
              }
            }
            rx += dx;
            ry += dy;
          }
        }
        else
        {
          // 16 colors
          int32_t palIdx = 0x200 + (((attr2 >> 12) & 0xF) * 16 * 2);
          for (int32_t i = x; i < x + rWidth; i++)
          {
            int32_t tx = rx >> 8;
            int32_t ty = ry >> 8;

            if ((i & 0x1ff) < 240 && tx >= 0 && tx < Width && ty >= 0 && ty < Height && true)
            {
              int32_t curIdx = (baseSprite + ((ty / 8) * pitch) + ((tx / 8) * scale)) * 32 + ((ty & 7) * 4) + ((tx & 7) / 2);
              int32_t lookup = processor->ReadU8(0x10000 + curIdx, vRamStart);
              if ((tx & 1) == 0)
              {
                lookup &= 0xf;
              }
              else
              {
                lookup >>= 4;
              }
              if (lookup != 0)
              {
                uint16_t pixelColor = processor->ReadU16(palIdx + lookup * 2, palRamStart);
                
                if ((Blend[i & 0x1ff] & blendTarget) != 0 && Blend[i & 0x1ff] != blendMaskType)
                {
                  uint16_t r = (uint8_t)((((pixelColor) & 0x1F) * blendA) >> 4);       //First 5 Bits
                  uint16_t g = (uint8_t)((((pixelColor >> 5) & 0x1F) * blendA) >> 4);  //Middle 5 Bits
                  uint16_t b = (uint8_t)((((pixelColor >> 10) & 0x1F) * blendA) >> 4);   //Last 5 Bits
                  uint16_t sourceValue = tft->dgetPixel(curLine, (i & 0x1ff));
                  r += (uint8_t)((((sourceValue >> 11) & 0x1F) * blendB) >> 4); //R
                  g += (uint8_t)((((sourceValue >> 5) & 0x3F) * blendB) >> 4); //G
                  b += (uint8_t)((((sourceValue) & 0x1F) * blendB) >> 4); //B
                  if (r > 0xff) r = 0xff;
                  if (g > 0xff) g = 0xff;
                  if (b > 0xff) b = 0xff;
                  pixelColor = ((uint8_t)(b) << 0) | ((uint8_t)(g) << 5) | ((uint8_t)(r) << 11);
                }
                else
                {
                  pixelColor = GBAToColor(pixelColor);
                }
                
                DrawPixel(curLine, (i & 0x1ff), pixelColor); 
                Blend[(i & 0x1ff)] = blendMaskType;
              }
            }
            rx += dx;
            ry += dy;
          }
        }
      }
    }
    else
    {
      if ((attr0 & (1 << 8)) == 0)
      {
        if ((attr1 & (1 << 13)) != 0) spritey = (Height - 1) - spritey;

        int32_t baseSprite;
        if ((dispCnt & (1 << 6)) != 0)
        {
          // 1 dimensional
          baseSprite = (attr2 & 0x3FF) + ((spritey / 8) * (Width / 8)) * scale;
        }
        else
        {
          // 2 dimensional
          baseSprite = (attr2 & 0x3FF) + ((spritey / 8) * 0x20);
        }

        int32_t baseInc = scale;
        if ((attr1 & (1 << 12)) != 0)
        {
          baseSprite += ((Width / 8) * scale) - scale;
          baseInc = -baseInc;
        }

        if ((attr0 & (1 << 13)) != 0)
        {
          // 256 colors
          for (int32_t i = x; i < x + Width; i++)
          {
            if ((i & 0x1ff) < 240 && true)
            {
              int32_t tx = (i - x) & 7;
              if ((attr1 & (1 << 12)) != 0) tx = 7 - tx;
              int32_t curIdx = baseSprite * 32 + ((spritey & 7) * 8) + tx;
              int32_t lookup = processor->ReadU8(0x10000 + curIdx, vRamStart);
              if (lookup != 0)
              {
                uint16_t pixelColor = GBAToColor(processor->ReadU16(0x200 + lookup * 2, palRamStart));
                DrawPixel(curLine, (i & 0x1ff), pixelColor); 
                Blend[(i & 0x1ff)] = blendMaskType;
              }
            }
            if (((i - x) & 7) == 7) baseSprite += baseInc;
          }
        }
        else
        {
          // 16 colors
          int32_t palIdx = 0x200 + (((attr2 >> 12) & 0xF) * 16 * 2);
          for (int32_t i = x; i < x + Width; i++)
          {
            if ((i & 0x1ff) < 240 && true)
            {
              int32_t tx = (i - x) & 7;
              if ((attr1 & (1 << 12)) != 0) tx = 7 - tx;
              int32_t curIdx = baseSprite * 32 + ((spritey & 7) * 4) + (tx / 2);
              int32_t lookup = processor->ReadU8(0x10000 + curIdx, vRamStart);
              if ((tx & 1) == 0)
              {
                lookup &= 0xf;
              }
              else
              {
                lookup >>= 4;
              }
              if (lookup != 0)
              {
                uint16_t pixelColor = GBAToColor(processor->ReadU16(palIdx + lookup * 2, palRamStart));
                DrawPixel(curLine, (i & 0x1ff), pixelColor); 
                Blend[(i & 0x1ff)] = blendMaskType;
              }
            }
            if (((i - x) & 7) == 7) baseSprite += baseInc;
          }
        }
      }
      else
      {
        int32_t rotScaleParam = (attr1 >> 9) & 0x1F;

        int16_t dx = (int16_t)processor->ReadU16Debug(OAM_BASE + (uint32_t)(rotScaleParam * 8 * 4) + 0x6);
        int16_t dmx = (int16_t)processor->ReadU16Debug(OAM_BASE + (uint32_t)(rotScaleParam * 8 * 4) + 0xE);
        int16_t dy = (int16_t)processor->ReadU16Debug(OAM_BASE + (uint32_t)(rotScaleParam * 8 * 4) + 0x16);
        int16_t dmy = (int16_t)processor->ReadU16Debug(OAM_BASE + (uint32_t)(rotScaleParam * 8 * 4) + 0x1E);

        int32_t cx = rWidth / 2;
        int32_t cy = rHeight / 2;

        int32_t baseSprite = attr2 & 0x3FF;
        int32_t pitch;

        if ((dispCnt & (1 << 6)) != 0)
        {
          // 1 dimensional
          pitch = (Width / 8) * scale;
        }
        else
        {
          // 2 dimensional
          pitch = 0x20;
        }

        int32_t rx = (int32_t)((dmx * (spritey - cy)) - (cx * dx) + (Width << 7));
        int32_t ry = (int32_t)((dmy * (spritey - cy)) - (cx * dy) + (Height << 7));

        // Draw a rot/scale sprite
        if ((attr0 & (1 << 13)) != 0)
        {
          // 256 colors
          for (int32_t i = x; i < x + rWidth; i++)
          {
            int32_t tx = rx >> 8;
            int32_t ty = ry >> 8;

            if ((i & 0x1ff) < 240 && tx >= 0 && tx < Width && ty >= 0 && ty < Height && true)
            {
              int32_t curIdx = (baseSprite + ((ty / 8) * pitch) + ((tx / 8) * scale)) * 32 + ((ty & 7) * 8) + (tx & 7);
              int32_t lookup = processor->ReadU8(0x10000 + curIdx, vRamStart);
              if (lookup != 0)
              {
                uint16_t pixelColor = GBAToColor(processor->ReadU16(0x200 + lookup * 2, palRamStart));
                DrawPixel(curLine, (i & 0x1ff), pixelColor); 
                Blend[(i & 0x1ff)] = blendMaskType;
              }
            }
            rx += dx;
            ry += dy;
          }
        }
        else
        {
          // 16 colors
          int32_t palIdx = 0x200 + (((attr2 >> 12) & 0xF) * 16 * 2);
          for (int32_t i = x; i < x + rWidth; i++)
          {
            int32_t tx = rx >> 8;
            int32_t ty = ry >> 8;

            if ((i & 0x1ff) < 240 && tx >= 0 && tx < Width && ty >= 0 && ty < Height && true)
            {
              int32_t curIdx = (baseSprite + ((ty / 8) * pitch) + ((tx / 8) * scale)) * 32 + ((ty & 7) * 4) + ((tx & 7) / 2);
              int32_t lookup = processor->ReadU8(0x10000 + curIdx, vRamStart);

              if ((tx & 1) == 0)
              {
                lookup &= 0xf;
              }
              else
              {
                lookup >>= 4;
              }
              if (lookup != 0)
              {
                uint16_t pixelColor = GBAToColor(processor->ReadU16(palIdx + lookup * 2, palRamStart));
                DrawPixel(curLine, (i & 0x1ff), pixelColor); 
                Blend[(i & 0x1ff)] = blendMaskType;
              }
            }
            rx += dx;
            ry += dy;
          }
        }
      }
    }
  }
}

void GBA::DrawSpritesBlend(int8_t priority)
{
  // OBJ must be enabled in this.dispCnt
  if ((dispCnt & (1 << 12)) == 0) return;

  uint8_t blendMaskType = (uint8_t)(1 << 4);

  for (int32_t oamNum = 127; oamNum >= 0; oamNum--)
  {
    uint16_t attr2 = processor->ReadU16Debug(OAM_BASE + (uint32_t)(oamNum * 8) + 4);

    if (((attr2 >> 10) & 3) != priority) continue;

    uint16_t attr0 = processor->ReadU16Debug(OAM_BASE + (uint32_t)(oamNum * 8) + 0);
    uint16_t attr1 = processor->ReadU16Debug(OAM_BASE + (uint32_t)(oamNum * 8) + 2);

    int32_t x = attr1 & 0x1FF;
    int32_t y = attr0 & 0xFF;

    bool semiTransparent = false;

    switch ((attr0 >> 10) & 3)
    {
    case 1:
      // Semi-transparent
      semiTransparent = true;
      break;
    case 2:
      // Obj window
      continue;
    case 3:
      continue;
    }

    if ((dispCnt & 0x7) >= 3 && (attr2 & 0x3FF) < 0x200) continue;
    
    int32_t Width = -1, Height = -1;
    switch ((attr0 >> 14) & 3)
    {
    case 0:
      // Square
      switch ((attr1 >> 14) & 3)
      {
      case 0: Width = 8; Height = 8; break;
      case 1: Width = 16; Height = 16; break;
      case 2: Width = 32; Height = 32; break;
      case 3: Width = 64; Height = 64; break;
      }
      break;
    case 1:
      // Horizontal Rectangle
      switch ((attr1 >> 14) & 3)
      {
      case 0: Width = 16; Height = 8; break;
      case 1: Width = 32; Height = 8; break;
      case 2: Width = 32; Height = 16; break;
      case 3: Width = 64; Height = 32; break;
      }
      break;
    case 2:
      // Vertical Rectangle
      switch ((attr1 >> 14) & 3)
      {
      case 0: Width = 8; Height = 16; break;
      case 1: Width = 8; Height = 32; break;
      case 2: Width = 16; Height = 32; break;
      case 3: Width = 32; Height = 64; break;
      }
      break;
    }

    // Check double size flag here

    int32_t rWidth = Width, rHeight = Height;
    if ((attr0 & (1 << 8)) != 0)
    {
      // Rot-scale on
      if ((attr0 & (1 << 9)) != 0)
      {
        rWidth *= 2;
        rHeight *= 2;
      }
    }
    else
    {
      // Invalid sprite
      if ((attr0 & (1 << 9)) != 0)
        Width = -1;
    }

    if (Width == -1)
    {
      // Invalid sprite
      continue;
    }

    // Y clipping
    if (y > ((y + rHeight) & 0xff))
    {
      if (curLine >= ((y + rHeight) & 0xff) && !(y < curLine)) continue;
    }
    else
    {
      if (curLine < y || curLine >= ((y + rHeight) & 0xff)) continue;
    }

    int32_t scale = 1;
    if ((attr0 & (1 << 13)) != 0) scale = 2;

    int32_t spritey = curLine - y;
    if (spritey < 0) spritey += 256;

    if (semiTransparent)
    {
      if ((attr0 & (1 << 8)) == 0)
      {
        if ((attr1 & (1 << 13)) != 0) spritey = (Height - 1) - spritey;

        int32_t baseSprite;
        if ((dispCnt & (1 << 6)) != 0)
        {
          // 1 dimensional
          baseSprite = (attr2 & 0x3FF) + ((spritey / 8) * (Width / 8)) * scale;
        }
        else
        {
          // 2 dimensional
          baseSprite = (attr2 & 0x3FF) + ((spritey / 8) * 0x20);
        }

        int32_t baseInc = scale;
        if ((attr1 & (1 << 12)) != 0)
        {
          baseSprite += ((Width / 8) * scale) - scale;
          baseInc = -baseInc;
        }

        if ((attr0 & (1 << 13)) != 0)
        {
          // 256 colors
          for (int32_t i = x; i < x + Width; i++)
          {
            if ((i & 0x1ff) < 240 && true)
            {
              int32_t tx = (i - x) & 7;
              if ((attr1 & (1 << 12)) != 0) tx = 7 - tx;
              int32_t curIdx = baseSprite * 32 + ((spritey & 7) * 8) + tx;
              int32_t lookup = processor->ReadU8(0x10000 + curIdx, vRamStart);
              if (lookup != 0)
              {
                uint16_t pixelColor = processor->ReadU16(0x200 + lookup * 2, palRamStart);
                
                if ((Blend[i & 0x1ff] & blendTarget) != 0 && Blend[i & 0x1ff] != blendMaskType)
                {
                  uint16_t r = (uint8_t)((((pixelColor) & 0x1F) * blendA) >> 4);       //First 5 Bits
                  uint16_t g = (uint8_t)((((pixelColor >> 5) & 0x1F) * blendA) >> 4);  //Middle 5 Bits
                  uint16_t b = (uint8_t)((((pixelColor >> 10) & 0x1F) * blendA) >> 4);   //Last 5 Bits
                  uint16_t sourceValue = tft->dgetPixel(curLine, (i & 0x1ff));
                  r += (uint8_t)((((sourceValue >> 11) & 0x1F) * blendB) >> 4); //R
                  g += (uint8_t)((((sourceValue >> 5) & 0x3F) * blendB) >> 4); //G
                  b += (uint8_t)((((sourceValue) & 0x1F) * blendB) >> 4); //B
                  if (r > 0xff) r = 0xff;
                  if (g > 0xff) g = 0xff;
                  if (b > 0xff) b = 0xff;
                  pixelColor = ((uint8_t)(b) << 0) | ((uint8_t)(g) << 5) | ((uint8_t)(r) << 11);
                }
                else
                {
                  pixelColor = GBAToColor(pixelColor);
                }
                
                DrawPixel(curLine, (i & 0x1ff), pixelColor); 
                Blend[(i & 0x1ff)] = blendMaskType;
              }
            }
            if (((i - x) & 7) == 7) baseSprite += baseInc;
          }
        }
        else
        {
          // 16 colors
          int32_t palIdx = 0x200 + (((attr2 >> 12) & 0xF) * 16 * 2);
          for (int32_t i = x; i < x + Width; i++)
          {
            if ((i & 0x1ff) < 240 && true)
            {
              int32_t tx = (i - x) & 7;
              if ((attr1 & (1 << 12)) != 0) tx = 7 - tx;
              int32_t curIdx = baseSprite * 32 + ((spritey & 7) * 4) + (tx / 2);
              int32_t lookup = processor->ReadU8(0x10000 + curIdx, vRamStart);
              if ((tx & 1) == 0)
              {
                lookup &= 0xf;
              }
              else
              {
                lookup >>= 4;
              }
              if (lookup != 0)
              {
                uint16_t pixelColor = processor->ReadU16(palIdx + lookup * 2, palRamStart);
                
                if ((Blend[i & 0x1ff] & blendTarget) != 0 && Blend[i & 0x1ff] != blendMaskType)
                {
                  uint16_t r = (uint8_t)((((pixelColor) & 0x1F) * blendA) >> 4);       //First 5 Bits
                  uint16_t g = (uint8_t)((((pixelColor >> 5) & 0x1F) * blendA) >> 4);  //Middle 5 Bits
                  uint16_t b = (uint8_t)((((pixelColor >> 10) & 0x1F) * blendA) >> 4);   //Last 5 Bits
                  uint16_t sourceValue = tft->dgetPixel(curLine, (i & 0x1ff));
                  r += (uint8_t)((((sourceValue >> 11) & 0x1F) * blendB) >> 4); //R
                  g += (uint8_t)((((sourceValue >> 5) & 0x3F) * blendB) >> 4); //G
                  b += (uint8_t)((((sourceValue) & 0x1F) * blendB) >> 4); //B
                  if (r > 0xff) r = 0xff;
                  if (g > 0xff) g = 0xff;
                  if (b > 0xff) b = 0xff;
                  pixelColor = ((uint8_t)(b) << 0) | ((uint8_t)(g) << 5) | ((uint8_t)(r) << 11);
                }
                else
                {
                  pixelColor = GBAToColor(pixelColor);
                }
                
                DrawPixel(curLine, (i & 0x1ff), pixelColor); 
                Blend[(i & 0x1ff)] = blendMaskType;
              }
            }
            if (((i - x) & 7) == 7) baseSprite += baseInc;
          }
        }
      }
      else
      {
        int32_t rotScaleParam = (attr1 >> 9) & 0x1F;

        int16_t dx = (int16_t)processor->ReadU16Debug(OAM_BASE + (uint32_t)(rotScaleParam * 8 * 4) + 0x6);
        int16_t dmx = (int16_t)processor->ReadU16Debug(OAM_BASE + (uint32_t)(rotScaleParam * 8 * 4) + 0xE);
        int16_t dy = (int16_t)processor->ReadU16Debug(OAM_BASE + (uint32_t)(rotScaleParam * 8 * 4) + 0x16);
        int16_t dmy = (int16_t)processor->ReadU16Debug(OAM_BASE + (uint32_t)(rotScaleParam * 8 * 4) + 0x1E);

        int32_t cx = rWidth / 2;
        int32_t cy = rHeight / 2;

        int32_t baseSprite = attr2 & 0x3FF;
        int32_t pitch;

        if ((dispCnt & (1 << 6)) != 0)
        {
          // 1 dimensional
          pitch = (Width / 8) * scale;
        }
        else
        {
          // 2 dimensional
          pitch = 0x20;
        }

        int32_t rx = (int32_t)((dmx * (spritey - cy)) - (cx * dx) + (Width << 7));
        int32_t ry = (int32_t)((dmy * (spritey - cy)) - (cx * dy) + (Height << 7));

        // Draw a rot/scale sprite
        if ((attr0 & (1 << 13)) != 0)
        {
          // 256 colors
          for (int32_t i = x; i < x + rWidth; i++)
          {
            int32_t tx = rx >> 8;
            int32_t ty = ry >> 8;

            if ((i & 0x1ff) < 240 && tx >= 0 && tx < Width && ty >= 0 && ty < Height && true)
            {
              int32_t curIdx = (baseSprite + ((ty / 8) * pitch) + ((tx / 8) * scale)) * 32 + ((ty & 7) * 8) + (tx & 7);
              int32_t lookup = processor->ReadU8(0x10000 + curIdx, vRamStart);
              if (lookup != 0)
              {
                uint16_t pixelColor = processor->ReadU16(0x200 + lookup * 2, palRamStart);
                
                if ((Blend[i & 0x1ff] & blendTarget) != 0 && Blend[i & 0x1ff] != blendMaskType)
                {
                  uint16_t r = (uint8_t)((((pixelColor) & 0x1F) * blendA) >> 4);       //First 5 Bits
                  uint16_t g = (uint8_t)((((pixelColor >> 5) & 0x1F) * blendA) >> 4);  //Middle 5 Bits
                  uint16_t b = (uint8_t)((((pixelColor >> 10) & 0x1F) * blendA) >> 4);   //Last 5 Bits
                  uint16_t sourceValue = tft->dgetPixel(curLine, (i & 0x1ff));
                  r += (uint8_t)((((sourceValue >> 11) & 0x1F) * blendB) >> 4); //R
                  g += (uint8_t)((((sourceValue >> 5) & 0x3F) * blendB) >> 4); //G
                  b += (uint8_t)((((sourceValue) & 0x1F) * blendB) >> 4); //B
                  if (r > 0xff) r = 0xff;
                  if (g > 0xff) g = 0xff;
                  if (b > 0xff) b = 0xff;
                  pixelColor = ((uint8_t)(b) << 0) | ((uint8_t)(g) << 5) | ((uint8_t)(r) << 11);
                }
                else
                {
                  pixelColor = GBAToColor(pixelColor);
                }
                
                DrawPixel(curLine, (i & 0x1ff), pixelColor); 
                Blend[(i & 0x1ff)] = blendMaskType;
              }
            }
            rx += dx;
            ry += dy;
          }
        }
        else
        {
          // 16 colors
          int32_t palIdx = 0x200 + (((attr2 >> 12) & 0xF) * 16 * 2);
          for (int32_t i = x; i < x + rWidth; i++)
          {
            int32_t tx = rx >> 8;
            int32_t ty = ry >> 8;

            if ((i & 0x1ff) < 240 && tx >= 0 && tx < Width && ty >= 0 && ty < Height && true)
            {
              int32_t curIdx = (baseSprite + ((ty / 8) * pitch) + ((tx / 8) * scale)) * 32 + ((ty & 7) * 4) + ((tx & 7) / 2);
              int32_t lookup = processor->ReadU8(0x10000 + curIdx, vRamStart);
              if ((tx & 1) == 0)
              {
                lookup &= 0xf;
              }
              else
              {
                lookup >>= 4;
              }
              if (lookup != 0)
              {
                uint16_t pixelColor = processor->ReadU16(palIdx + lookup * 2, palRamStart);
                
                if ((Blend[i & 0x1ff] & blendTarget) != 0 && Blend[i & 0x1ff] != blendMaskType)
                {
                  uint16_t r = (uint8_t)((((pixelColor) & 0x1F) * blendA) >> 4);       //First 5 Bits
                  uint16_t g = (uint8_t)((((pixelColor >> 5) & 0x1F) * blendA) >> 4);  //Middle 5 Bits
                  uint16_t b = (uint8_t)((((pixelColor >> 10) & 0x1F) * blendA) >> 4);   //Last 5 Bits
                  uint16_t sourceValue = tft->dgetPixel(curLine, (i & 0x1ff));
                  r += (uint8_t)((((sourceValue >> 11) & 0x1F) * blendB) >> 4); //R
                  g += (uint8_t)((((sourceValue >> 5) & 0x3F) * blendB) >> 4); //G
                  b += (uint8_t)((((sourceValue) & 0x1F) * blendB) >> 4); //B
                  if (r > 0xff) r = 0xff;
                  if (g > 0xff) g = 0xff;
                  if (b > 0xff) b = 0xff;
                  pixelColor = ((uint8_t)(b) << 0) | ((uint8_t)(g) << 5) | ((uint8_t)(r) << 11);
                }
                else
                {
                  pixelColor = GBAToColor(pixelColor);
                }
                
                DrawPixel(curLine, (i & 0x1ff), pixelColor); 
                Blend[(i & 0x1ff)] = blendMaskType;
              }
            }
            rx += dx;
            ry += dy;
          }
        }
      }
    }
    else
    {
      if ((attr0 & (1 << 8)) == 0)
      {
        if ((attr1 & (1 << 13)) != 0) spritey = (Height - 1) - spritey;

        int32_t baseSprite;
        if ((dispCnt & (1 << 6)) != 0)
        {
          // 1 dimensional
          baseSprite = (attr2 & 0x3FF) + ((spritey / 8) * (Width / 8)) * scale;
        }
        else
        {
          // 2 dimensional
          baseSprite = (attr2 & 0x3FF) + ((spritey / 8) * 0x20);
        }

        int32_t baseInc = scale;
        if ((attr1 & (1 << 12)) != 0)
        {
          baseSprite += ((Width / 8) * scale) - scale;
          baseInc = -baseInc;
        }

        if ((attr0 & (1 << 13)) != 0)
        {
          // 256 colors
          for (int32_t i = x; i < x + Width; i++)
          {
            if ((i & 0x1ff) < 240 && true)
            {
              int32_t tx = (i - x) & 7;
              if ((attr1 & (1 << 12)) != 0) tx = 7 - tx;
              int32_t curIdx = baseSprite * 32 + ((spritey & 7) * 8) + tx;
              int32_t lookup = processor->ReadU8(0x10000 + curIdx, vRamStart);
              if (lookup != 0)
              {
                uint16_t pixelColor = processor->ReadU16(0x200 + lookup * 2, palRamStart);
                
                if ((Blend[i & 0x1ff] & blendTarget) != 0 && Blend[i & 0x1ff] != blendMaskType)
                {
                  uint16_t r = (uint8_t)((((pixelColor) & 0x1F) * blendA) >> 4);       //First 5 Bits
                  uint16_t g = (uint8_t)((((pixelColor >> 5) & 0x1F) * blendA) >> 4);  //Middle 5 Bits
                  uint16_t b = (uint8_t)((((pixelColor >> 10) & 0x1F) * blendA) >> 4);   //Last 5 Bits
                  uint16_t sourceValue = tft->dgetPixel(curLine, (i & 0x1ff));
                  r += (uint8_t)((((sourceValue >> 11) & 0x1F) * blendB) >> 4); //R
                  g += (uint8_t)((((sourceValue >> 5) & 0x3F) * blendB) >> 4); //G
                  b += (uint8_t)((((sourceValue) & 0x1F) * blendB) >> 4); //B
                  if (r > 0xff) r = 0xff;
                  if (g > 0xff) g = 0xff;
                  if (b > 0xff) b = 0xff;
                  pixelColor = ((uint8_t)(b) << 0) | ((uint8_t)(g) << 5) | ((uint8_t)(r) << 11);
                }
                else
                {
                  pixelColor = GBAToColor(pixelColor);
                }
                
                DrawPixel(curLine, (i & 0x1ff), pixelColor); 
                Blend[(i & 0x1ff)] = blendMaskType;
              }
            }
            if (((i - x) & 7) == 7) baseSprite += baseInc;
          }
        }
        else
        {
          // 16 colors
          int32_t palIdx = 0x200 + (((attr2 >> 12) & 0xF) * 16 * 2);
          for (int32_t i = x; i < x + Width; i++)
          {
            if ((i & 0x1ff) < 240 && true)
            {
              int32_t tx = (i - x) & 7;
              if ((attr1 & (1 << 12)) != 0) tx = 7 - tx;
              int32_t curIdx = baseSprite * 32 + ((spritey & 7) * 4) + (tx / 2);
              int32_t lookup = processor->ReadU8(0x10000 + curIdx, vRamStart);
              if ((tx & 1) == 0)
              {
                lookup &= 0xf;
              }
              else
              {
                lookup >>= 4;
              }
              if (lookup != 0)
              {
                uint16_t pixelColor = processor->ReadU16(palIdx + lookup * 2, palRamStart);
                
                if ((Blend[i & 0x1ff] & blendTarget) != 0 && Blend[i & 0x1ff] != blendMaskType)
                {
                  uint16_t r = (uint8_t)((((pixelColor) & 0x1F) * blendA) >> 4);       //First 5 Bits
                  uint16_t g = (uint8_t)((((pixelColor >> 5) & 0x1F) * blendA) >> 4);  //Middle 5 Bits
                  uint16_t b = (uint8_t)((((pixelColor >> 10) & 0x1F) * blendA) >> 4);   //Last 5 Bits
                  uint16_t sourceValue = tft->dgetPixel(curLine, (i & 0x1ff));
                  r += (uint8_t)((((sourceValue >> 11) & 0x1F) * blendB) >> 4); //R
                  g += (uint8_t)((((sourceValue >> 5) & 0x3F) * blendB) >> 4); //G
                  b += (uint8_t)((((sourceValue) & 0x1F) * blendB) >> 4); //B
                  if (r > 0xff) r = 0xff;
                  if (g > 0xff) g = 0xff;
                  if (b > 0xff) b = 0xff;
                  pixelColor = ((uint8_t)(b) << 0) | ((uint8_t)(g) << 5) | ((uint8_t)(r) << 11);
                }
                else
                {
                  pixelColor = GBAToColor(pixelColor);
                }
                
                DrawPixel(curLine, (i & 0x1ff), pixelColor); 
                Blend[(i & 0x1ff)] = blendMaskType;
              }
            }
            if (((i - x) & 7) == 7) baseSprite += baseInc;
          }
        }
      }
      else
      {
        int32_t rotScaleParam = (attr1 >> 9) & 0x1F;

        int16_t dx = (int16_t)processor->ReadU16Debug(OAM_BASE + (uint32_t)(rotScaleParam * 8 * 4) + 0x6);
        int16_t dmx = (int16_t)processor->ReadU16Debug(OAM_BASE + (uint32_t)(rotScaleParam * 8 * 4) + 0xE);
        int16_t dy = (int16_t)processor->ReadU16Debug(OAM_BASE + (uint32_t)(rotScaleParam * 8 * 4) + 0x16);
        int16_t dmy = (int16_t)processor->ReadU16Debug(OAM_BASE + (uint32_t)(rotScaleParam * 8 * 4) + 0x1E);

        int32_t cx = rWidth / 2;
        int32_t cy = rHeight / 2;

        int32_t baseSprite = attr2 & 0x3FF;
        int32_t pitch;

        if ((dispCnt & (1 << 6)) != 0)
        {
          // 1 dimensional
          pitch = (Width / 8) * scale;
        }
        else
        {
          // 2 dimensional
          pitch = 0x20;
        }

        int32_t rx = (int32_t)((dmx * (spritey - cy)) - (cx * dx) + (Width << 7));
        int32_t ry = (int32_t)((dmy * (spritey - cy)) - (cx * dy) + (Height << 7));

        // Draw a rot/scale sprite
        if ((attr0 & (1 << 13)) != 0)
        {
          // 256 colors
          for (int32_t i = x; i < x + rWidth; i++)
          {
            int32_t tx = rx >> 8;
            int32_t ty = ry >> 8;

            if ((i & 0x1ff) < 240 && tx >= 0 && tx < Width && ty >= 0 && ty < Height && true)
            {
              int32_t curIdx = (baseSprite + ((ty / 8) * pitch) + ((tx / 8) * scale)) * 32 + ((ty & 7) * 8) + (tx & 7);
              int32_t lookup = processor->ReadU8(0x10000 + curIdx, vRamStart);
              if (lookup != 0)
              {
                uint16_t pixelColor = processor->ReadU16(0x200 + lookup * 2, palRamStart);
                
                if ((Blend[i & 0x1ff] & blendTarget) != 0 && Blend[i & 0x1ff] != blendMaskType)
                {
                  uint16_t r = (uint8_t)((((pixelColor) & 0x1F) * blendA) >> 4);       //First 5 Bits
                  uint16_t g = (uint8_t)((((pixelColor >> 5) & 0x1F) * blendA) >> 4);  //Middle 5 Bits
                  uint16_t b = (uint8_t)((((pixelColor >> 10) & 0x1F) * blendA) >> 4);   //Last 5 Bits
                  uint16_t sourceValue = tft->dgetPixel(curLine, (i & 0x1ff));
                  r += (uint8_t)((((sourceValue >> 11) & 0x1F) * blendB) >> 4); //R
                  g += (uint8_t)((((sourceValue >> 5) & 0x3F) * blendB) >> 4); //G
                  b += (uint8_t)((((sourceValue) & 0x1F) * blendB) >> 4); //B
                  if (r > 0xff) r = 0xff;
                  if (g > 0xff) g = 0xff;
                  if (b > 0xff) b = 0xff;
                  pixelColor = ((uint8_t)(b) << 0) | ((uint8_t)(g) << 5) | ((uint8_t)(r) << 11);
                }
                else
                {
                  pixelColor = GBAToColor(pixelColor);
                }
              
                DrawPixel(curLine, (i & 0x1ff), pixelColor); 
                Blend[(i & 0x1ff)] = blendMaskType;
              }
            }
            rx += dx;
            ry += dy;
          }
        }
        else
        {
          // 16 colors
          int32_t palIdx = 0x200 + (((attr2 >> 12) & 0xF) * 16 * 2);
          for (int32_t i = x; i < x + rWidth; i++)
          {
            int32_t tx = rx >> 8;
            int32_t ty = ry >> 8;

            if ((i & 0x1ff) < 240 && tx >= 0 && tx < Width && ty >= 0 && ty < Height && true)
            {
              int32_t curIdx = (baseSprite + ((ty / 8) * pitch) + ((tx / 8) * scale)) * 32 + ((ty & 7) * 4) + ((tx & 7) / 2);
              int32_t lookup = processor->ReadU8(0x10000 + curIdx, vRamStart);
              if ((tx & 1) == 0)
              {
                lookup &= 0xf;
              }
              else
              {
                lookup >>= 4;
              }
              if (lookup != 0)
              {
                uint16_t pixelColor = processor->ReadU16(palIdx + lookup * 2, palRamStart);
                
                if ((Blend[i & 0x1ff] & blendTarget) != 0 && Blend[i & 0x1ff] != blendMaskType)
                {
                  uint16_t r = (uint8_t)((((pixelColor) & 0x1F) * blendA) >> 4);       //First 5 Bits
                  uint16_t g = (uint8_t)((((pixelColor >> 5) & 0x1F) * blendA) >> 4);  //Middle 5 Bits
                  uint16_t b = (uint8_t)((((pixelColor >> 10) & 0x1F) * blendA) >> 4);   //Last 5 Bits
                  uint16_t sourceValue = tft->dgetPixel(curLine, (i & 0x1ff));
                  r += (uint8_t)((((sourceValue >> 11) & 0x1F) * blendB) >> 4); //R
                  g += (uint8_t)((((sourceValue >> 5) & 0x3F) * blendB) >> 4); //G
                  b += (uint8_t)((((sourceValue) & 0x1F) * blendB) >> 4); //B
                  if (r > 0xff) r = 0xff;
                  if (g > 0xff) g = 0xff;
                  if (b > 0xff) b = 0xff;
                  pixelColor = ((uint8_t)(b) << 0) | ((uint8_t)(g) << 5) | ((uint8_t)(r) << 11);
                }
                else
                {
                  pixelColor = GBAToColor(pixelColor);
                }
                
                DrawPixel(curLine, (i & 0x1ff), pixelColor); 
                Blend[(i & 0x1ff)] = blendMaskType;
              }
            }
            rx += dx;
            ry += dy;
          }
        }
      }
    }
  }
}

void GBA::DrawSpritesBrightInc(int32_t priority)
{
  // OBJ must be enabled in this.dispCnt
  if ((dispCnt & (1 << 12)) == 0) return;

  uint8_t blendMaskType = (uint8_t)(1 << 4);

  for (int32_t oamNum = 127; oamNum >= 0; oamNum--)
  {
    uint16_t attr2 = processor->ReadU16Debug(OAM_BASE + (uint32_t)(oamNum * 8) + 4);

    if (((attr2 >> 10) & 3) != priority) continue;

    uint16_t attr0 = processor->ReadU16Debug(OAM_BASE + (uint32_t)(oamNum * 8) + 0);
    uint16_t attr1 = processor->ReadU16Debug(OAM_BASE + (uint32_t)(oamNum * 8) + 2);

    int32_t x = attr1 & 0x1FF;
    int32_t y = attr0 & 0xFF;

    bool semiTransparent = false;

    switch ((attr0 >> 10) & 3)
    {
    case 1:
      // Semi-transparent
      semiTransparent = true;
      break;
    case 2:
      // Obj window
      continue;
    case 3:
      continue;
    }

    if ((dispCnt & 0x7) >= 3 && (attr2 & 0x3FF) < 0x200) continue;

    int32_t Width = -1, Height = -1;
    switch ((attr0 >> 14) & 3)
    {
    case 0:
      // Square
      switch ((attr1 >> 14) & 3)
      {
      case 0: Width = 8; Height = 8; break;
      case 1: Width = 16; Height = 16; break;
      case 2: Width = 32; Height = 32; break;
      case 3: Width = 64; Height = 64; break;
      }
      break;
    case 1:
      // Horizontal Rectangle
      switch ((attr1 >> 14) & 3)
      {
      case 0: Width = 16; Height = 8; break;
      case 1: Width = 32; Height = 8; break;
      case 2: Width = 32; Height = 16; break;
      case 3: Width = 64; Height = 32; break;
      }
      break;
    case 2:
      // Vertical Rectangle
      switch ((attr1 >> 14) & 3)
      {
      case 0: Width = 8; Height = 16; break;
      case 1: Width = 8; Height = 32; break;
      case 2: Width = 16; Height = 32; break;
      case 3: Width = 32; Height = 64; break;
      }
      break;
    }

    // Check double size flag here

    int32_t rWidth = Width, rHeight = Height;
    if ((attr0 & (1 << 8)) != 0)
    {
      // Rot-scale on
      if ((attr0 & (1 << 9)) != 0)
      {
        rWidth *= 2;
        rHeight *= 2;
      }
    }
    else
    {
      // Invalid sprite
      if ((attr0 & (1 << 9)) != 0)
        Width = -1;
    }

    if (Width == -1)
    {
      // Invalid sprite
      continue;
    }

    // Y clipping
    if (y > ((y + rHeight) & 0xff))
    {
      if (curLine >= ((y + rHeight) & 0xff) && !(y < curLine)) continue;
    }
    else
    {
      if (curLine < y || curLine >= ((y + rHeight) & 0xff)) continue;
    }

    int32_t scale = 1;
    if ((attr0 & (1 << 13)) != 0) scale = 2;

    int32_t spritey = curLine - y;
    if (spritey < 0) spritey += 256;

    if (semiTransparent)
    {
      if ((attr0 & (1 << 8)) == 0)
      {
        if ((attr1 & (1 << 13)) != 0) spritey = (Height - 1) - spritey;

        int32_t baseSprite;
        if ((dispCnt & (1 << 6)) != 0)
        {
          // 1 dimensional
          baseSprite = (attr2 & 0x3FF) + ((spritey / 8) * (Width / 8)) * scale;
        }
        else
        {
          // 2 dimensional
          baseSprite = (attr2 & 0x3FF) + ((spritey / 8) * 0x20);
        }

        int32_t baseInc = scale;
        if ((attr1 & (1 << 12)) != 0)
        {
          baseSprite += ((Width / 8) * scale) - scale;
          baseInc = -baseInc;
        }

        if ((attr0 & (1 << 13)) != 0)
        {
          // 256 colors
          for (int32_t i = x; i < x + Width; i++)
          {
            if ((i & 0x1ff) < 240 && true)
            {
              int32_t tx = (i - x) & 7;
              if ((attr1 & (1 << 12)) != 0) tx = 7 - tx;
              int32_t curIdx = baseSprite * 32 + ((spritey & 7) * 8) + tx;
              int32_t lookup = processor->ReadU8(0x10000 + curIdx, vRamStart);
              if (lookup != 0)
              {
                uint16_t pixelColor = processor->ReadU16(0x200 + lookup * 2, palRamStart);
                
                if ((Blend[i & 0x1ff] & blendTarget) != 0 && Blend[i & 0x1ff] != blendMaskType)
                {
                  uint16_t r = (uint8_t)((((pixelColor) & 0x1F) * blendA) >> 4);       //First 5 Bits
                  uint16_t g = (uint8_t)((((pixelColor >> 5) & 0x1F) * blendA) >> 4);  //Middle 5 Bits
                  uint16_t b = (uint8_t)((((pixelColor >> 10) & 0x1F) * blendA) >> 4);   //Last 5 Bits
                  uint16_t sourceValue = tft->dgetPixel(curLine, (i & 0x1ff));
                  r += (uint8_t)((((sourceValue >> 11) & 0x1F) * blendB) >> 4); //R
                  g += (uint8_t)((((sourceValue >> 5) & 0x3F) * blendB) >> 4); //G
                  b += (uint8_t)((((sourceValue) & 0x1F) * blendB) >> 4); //B
                  if (r > 0xff) r = 0xff;
                  if (g > 0xff) g = 0xff;
                  if (b > 0xff) b = 0xff;
                  pixelColor = ((uint8_t)(b) << 0) | ((uint8_t)(g) << 5) | ((uint8_t)(r) << 11);
                }
                else
                {
                  pixelColor = GBAToColor(pixelColor);
                }
                
                DrawPixel(curLine, (i & 0x1ff), pixelColor); 
                Blend[(i & 0x1ff)] = blendMaskType;
              }
            }
            if (((i - x) & 7) == 7) baseSprite += baseInc;
          }
        }
        else
        {
          // 16 colors
          int32_t palIdx = 0x200 + (((attr2 >> 12) & 0xF) * 16 * 2);
          for (int32_t i = x; i < x + Width; i++)
          {
            if ((i & 0x1ff) < 240 && true)
            {
              int32_t tx = (i - x) & 7;
              if ((attr1 & (1 << 12)) != 0) tx = 7 - tx;
              int32_t curIdx = baseSprite * 32 + ((spritey & 7) * 4) + (tx / 2);
              int32_t lookup = processor->ReadU8(0x10000 + curIdx, vRamStart);
              if ((tx & 1) == 0)
              {
                lookup &= 0xf;
              }
              else
              {
                lookup >>= 4;
              }
              if (lookup != 0)
              {
                uint16_t pixelColor = processor->ReadU16(palIdx + lookup * 2, palRamStart);
                
                if ((Blend[i & 0x1ff] & blendTarget) != 0 && Blend[i & 0x1ff] != blendMaskType)
                {
                  uint16_t r = (uint8_t)((((pixelColor) & 0x1F) * blendA) >> 4);       //First 5 Bits
                  uint16_t g = (uint8_t)((((pixelColor >> 5) & 0x1F) * blendA) >> 4);  //Middle 5 Bits
                  uint16_t b = (uint8_t)((((pixelColor >> 10) & 0x1F) * blendA) >> 4);   //Last 5 Bits
                  uint16_t sourceValue = tft->dgetPixel(curLine, (i & 0x1ff));
                  r += (uint8_t)((((sourceValue >> 11) & 0x1F) * blendB) >> 4); //R
                  g += (uint8_t)((((sourceValue >> 5) & 0x3F) * blendB) >> 4); //G
                  b += (uint8_t)((((sourceValue) & 0x1F) * blendB) >> 4); //B
                  if (r > 0xff) r = 0xff;
                  if (g > 0xff) g = 0xff;
                  if (b > 0xff) b = 0xff;
                  pixelColor = ((uint8_t)(b) << 0) | ((uint8_t)(g) << 5) | ((uint8_t)(r) << 11);
                }
                else
                {
                  pixelColor = GBAToColor(pixelColor);
                }
                
                DrawPixel(curLine, (i & 0x1ff), pixelColor); 
                Blend[(i & 0x1ff)] = blendMaskType;
              }
            }
            if (((i - x) & 7) == 7) baseSprite += baseInc;
          }
        }
      }
      else
      {
        int32_t rotScaleParam = (attr1 >> 9) & 0x1F;

        int16_t dx = (int16_t)processor->ReadU16Debug(OAM_BASE + (uint32_t)(rotScaleParam * 8 * 4) + 0x6);
        int16_t dmx = (int16_t)processor->ReadU16Debug(OAM_BASE + (uint32_t)(rotScaleParam * 8 * 4) + 0xE);
        int16_t dy = (int16_t)processor->ReadU16Debug(OAM_BASE + (uint32_t)(rotScaleParam * 8 * 4) + 0x16);
        int16_t dmy = (int16_t)processor->ReadU16Debug(OAM_BASE + (uint32_t)(rotScaleParam * 8 * 4) + 0x1E);

        int32_t cx = rWidth / 2;
        int32_t cy = rHeight / 2;

        int32_t baseSprite = attr2 & 0x3FF;
        int32_t pitch;

        if ((dispCnt & (1 << 6)) != 0)
        {
          // 1 dimensional
          pitch = (Width / 8) * scale;
        }
        else
        {
          // 2 dimensional
          pitch = 0x20;
        }

        int32_t rx = (int32_t)((dmx * (spritey - cy)) - (cx * dx) + (Width << 7));
        int32_t ry = (int32_t)((dmy * (spritey - cy)) - (cx * dy) + (Height << 7));

        // Draw a rot/scale sprite
        if ((attr0 & (1 << 13)) != 0)
        {
          // 256 colors
          for (int32_t i = x; i < x + rWidth; i++)
          {
            int32_t tx = rx >> 8;
            int32_t ty = ry >> 8;

            if ((i & 0x1ff) < 240 && tx >= 0 && tx < Width && ty >= 0 && ty < Height && true)
            {
              int32_t curIdx = (baseSprite + ((ty / 8) * pitch) + ((tx / 8) * scale)) * 32 + ((ty & 7) * 8) + (tx & 7);
              int32_t lookup = processor->ReadU8(0x10000 + curIdx, vRamStart);
              if (lookup != 0)
              {
                uint16_t pixelColor = processor->ReadU16(0x200 + lookup * 2, palRamStart);
                
                if ((Blend[i & 0x1ff] & blendTarget) != 0 && Blend[i & 0x1ff] != blendMaskType)
                {
                  uint16_t r = (uint8_t)((((pixelColor) & 0x1F) * blendA) >> 4);       //First 5 Bits
                  uint16_t g = (uint8_t)((((pixelColor >> 5) & 0x1F) * blendA) >> 4);  //Middle 5 Bits
                  uint16_t b = (uint8_t)((((pixelColor >> 10) & 0x1F) * blendA) >> 4);   //Last 5 Bits
                  uint16_t sourceValue = tft->dgetPixel(curLine, (i & 0x1ff));
                  r += (uint8_t)((((sourceValue >> 11) & 0x1F) * blendB) >> 4); //R
                  g += (uint8_t)((((sourceValue >> 5) & 0x3F) * blendB) >> 4); //G
                  b += (uint8_t)((((sourceValue) & 0x1F) * blendB) >> 4); //B
                  if (r > 0xff) r = 0xff;
                  if (g > 0xff) g = 0xff;
                  if (b > 0xff) b = 0xff;
                  pixelColor = ((uint8_t)(b) << 0) | ((uint8_t)(g) << 5) | ((uint8_t)(r) << 11);
                }
                else
                {
                  pixelColor = GBAToColor(pixelColor);
                }
                
                DrawPixel(curLine, (i & 0x1ff), pixelColor); 
                Blend[(i & 0x1ff)] = blendMaskType;
              }
            }
            rx += dx;
            ry += dy;
          }
        }
        else
        {
          // 16 colors
          int32_t palIdx = 0x200 + (((attr2 >> 12) & 0xF) * 16 * 2);
          for (int32_t i = x; i < x + rWidth; i++)
          {
            int32_t tx = rx >> 8;
            int32_t ty = ry >> 8;

            if ((i & 0x1ff) < 240 && tx >= 0 && tx < Width && ty >= 0 && ty < Height && true)
            {
              int32_t curIdx = (baseSprite + ((ty / 8) * pitch) + ((tx / 8) * scale)) * 32 + ((ty & 7) * 4) + ((tx & 7) / 2);
              int32_t lookup = processor->ReadU8(0x10000 + curIdx, vRamStart);
              if ((tx & 1) == 0)
              {
                lookup &= 0xf;
              }
              else
              {
                lookup >>= 4;
              }
              if (lookup != 0)
              {
                uint16_t pixelColor = processor->ReadU16(palIdx + lookup * 2, palRamStart);
                
                if ((Blend[i & 0x1ff] & blendTarget) != 0 && Blend[i & 0x1ff] != blendMaskType)
                {
                  uint16_t r = (uint8_t)((((pixelColor) & 0x1F) * blendA) >> 4);       //First 5 Bits
                  uint16_t g = (uint8_t)((((pixelColor >> 5) & 0x1F) * blendA) >> 4);  //Middle 5 Bits
                  uint16_t b = (uint8_t)((((pixelColor >> 10) & 0x1F) * blendA) >> 4);   //Last 5 Bits
                  uint16_t sourceValue = tft->dgetPixel(curLine, (i & 0x1ff));
                  r += (uint8_t)((((sourceValue >> 11) & 0x1F) * blendB) >> 4); //R
                  g += (uint8_t)((((sourceValue >> 5) & 0x3F) * blendB) >> 4); //G
                  b += (uint8_t)((((sourceValue) & 0x1F) * blendB) >> 4); //B
                  if (r > 0xff) r = 0xff;
                  if (g > 0xff) g = 0xff;
                  if (b > 0xff) b = 0xff;
                  pixelColor = ((uint8_t)(b) << 0) | ((uint8_t)(g) << 5) | ((uint8_t)(r) << 11);
                }
                else
                {
                  pixelColor = GBAToColor(pixelColor);
                }
                
                DrawPixel(curLine, (i & 0x1ff), pixelColor); 
                Blend[(i & 0x1ff)] = blendMaskType;
              }
            }
            rx += dx;
            ry += dy;
          }
        }
      }
    }
    else
    {
      if ((attr0 & (1 << 8)) == 0)
      {
        if ((attr1 & (1 << 13)) != 0) spritey = (Height - 1) - spritey;

        int32_t baseSprite;
        if ((dispCnt & (1 << 6)) != 0)
        {
          // 1 dimensional
          baseSprite = (attr2 & 0x3FF) + ((spritey / 8) * (Width / 8)) * scale;
        }
        else
        {
          // 2 dimensional
          baseSprite = (attr2 & 0x3FF) + ((spritey / 8) * 0x20);
        }

        int32_t baseInc = scale;
        if ((attr1 & (1 << 12)) != 0)
        {
          baseSprite += ((Width / 8) * scale) - scale;
          baseInc = -baseInc;
        }

        if ((attr0 & (1 << 13)) != 0)
        {
          // 256 colors
          for (int32_t i = x; i < x + Width; i++)
          {
            if ((i & 0x1ff) < 240 && true)
            {
              int32_t tx = (i - x) & 7;
              if ((attr1 & (1 << 12)) != 0) tx = 7 - tx;
              int32_t curIdx = baseSprite * 32 + ((spritey & 7) * 8) + tx;
              int32_t lookup = processor->ReadU8(0x10000 + curIdx, vRamStart);
              if (lookup != 0)
              {
          uint16_t pixelColor = processor->ReadU16(0x200 + lookup * 2, palRamStart);
                uint16_t r = (uint8_t)((pixelColor) & 0x1F);       //First 5 Bits
                uint16_t g = (uint8_t)((pixelColor >> 5) & 0x1F);  //Middle 5 Bits
                uint16_t b = (uint8_t)((pixelColor >> 10) & 0x1F);   //Last 5 Bits
                r = r + (((0x1F - r) * blendY) >> 4);
                g = g + (((0x1F - g) * blendY) >> 4);
                b = b + (((0x1F - b) * blendY) >> 4);
                pixelColor = ((uint8_t)(b) << 0) | ((uint8_t)(g) << 5) | ((uint8_t)(r) << 11);
                DrawPixel(curLine, (i & 0x1ff), pixelColor); 
                Blend[(i & 0x1ff)] = blendMaskType;
              }
            }
            if (((i - x) & 7) == 7) baseSprite += baseInc;
          }
        }
        else
        {
          // 16 colors
          int32_t palIdx = 0x200 + (((attr2 >> 12) & 0xF) * 16 * 2);
          for (int32_t i = x; i < x + Width; i++)
          {
            if ((i & 0x1ff) < 240 && true)
            {
              int32_t tx = (i - x) & 7;
              if ((attr1 & (1 << 12)) != 0) tx = 7 - tx;
              int32_t curIdx = baseSprite * 32 + ((spritey & 7) * 4) + (tx / 2);
              int32_t lookup = processor->ReadU8(0x10000 + curIdx, vRamStart);
              if ((tx & 1) == 0)
              {
                lookup &= 0xf;
              }
              else
              {
                lookup >>= 4;
              }
              if (lookup != 0)
              {
          uint16_t pixelColor = processor->ReadU16(palIdx + lookup * 2, palRamStart);
                uint16_t r = (uint8_t)((pixelColor) & 0x1F);       //First 5 Bits
                uint16_t g = (uint8_t)((pixelColor >> 5) & 0x1F);  //Middle 5 Bits
                uint16_t b = (uint8_t)((pixelColor >> 10) & 0x1F);   //Last 5 Bits
                r = r + (((0x1F - r) * blendY) >> 4);
                g = g + (((0x1F - g) * blendY) >> 4);
                b = b + (((0x1F - b) * blendY) >> 4);
                pixelColor = ((uint8_t)(b) << 0) | ((uint8_t)(g) << 5) | ((uint8_t)(r) << 11);
                DrawPixel(curLine, (i & 0x1ff), pixelColor); 
                Blend[(i & 0x1ff)] = blendMaskType;
              }
            }
            if (((i - x) & 7) == 7) baseSprite += baseInc;
          }
        }
      }
      else
      {
        int32_t rotScaleParam = (attr1 >> 9) & 0x1F;

        int16_t dx = (int16_t)processor->ReadU16Debug(OAM_BASE + (uint32_t)(rotScaleParam * 8 * 4) + 0x6);
        int16_t dmx = (int16_t)processor->ReadU16Debug(OAM_BASE + (uint32_t)(rotScaleParam * 8 * 4) + 0xE);
        int16_t dy = (int16_t)processor->ReadU16Debug(OAM_BASE + (uint32_t)(rotScaleParam * 8 * 4) + 0x16);
        int16_t dmy = (int16_t)processor->ReadU16Debug(OAM_BASE + (uint32_t)(rotScaleParam * 8 * 4) + 0x1E);

        int32_t cx = rWidth / 2;
        int32_t cy = rHeight / 2;

        int32_t baseSprite = attr2 & 0x3FF;
        int32_t pitch;

        if ((dispCnt & (1 << 6)) != 0)
        {
          // 1 dimensional
          pitch = (Width / 8) * scale;
        }
        else
        {
          // 2 dimensional
          pitch = 0x20;
        }

        int32_t rx = (int32_t)((dmx * (spritey - cy)) - (cx * dx) + (Width << 7));
        int32_t ry = (int32_t)((dmy * (spritey - cy)) - (cx * dy) + (Height << 7));

        // Draw a rot/scale sprite
        if ((attr0 & (1 << 13)) != 0)
        {
          // 256 colors
          for (int32_t i = x; i < x + rWidth; i++)
          {
            int32_t tx = rx >> 8;
            int32_t ty = ry >> 8;

            if ((i & 0x1ff) < 240 && tx >= 0 && tx < Width && ty >= 0 && ty < Height && true)
            {
              int32_t curIdx = (baseSprite + ((ty / 8) * pitch) + ((tx / 8) * scale)) * 32 + ((ty & 7) * 8) + (tx & 7);
              int32_t lookup = processor->ReadU8(0x10000 + curIdx, vRamStart);
              if (lookup != 0)
              {
          uint16_t pixelColor = processor->ReadU16(0x200 + lookup * 2, palRamStart);
                uint16_t r = (uint8_t)((pixelColor) & 0x1F);       //First 5 Bits
                uint16_t g = (uint8_t)((pixelColor >> 5) & 0x1F);  //Middle 5 Bits
                uint16_t b = (uint8_t)((pixelColor >> 10) & 0x1F);   //Last 5 Bits
                r = r + (((0x1F - r) * blendY) >> 4);
                g = g + (((0x1F - g) * blendY) >> 4);
                b = b + (((0x1F - b) * blendY) >> 4);
                pixelColor = ((uint8_t)(b) << 0) | ((uint8_t)(g) << 5) | ((uint8_t)(r) << 11);
                DrawPixel(curLine, (i & 0x1ff), pixelColor); 
                Blend[(i & 0x1ff)] = blendMaskType;
              }
            }
            rx += dx;
            ry += dy;
          }
        }
        else
        {
          // 16 colors
          int32_t palIdx = 0x200 + (((attr2 >> 12) & 0xF) * 16 * 2);
          for (int32_t i = x; i < x + rWidth; i++)
          {
            int32_t tx = rx >> 8;
            int32_t ty = ry >> 8;

            if ((i & 0x1ff) < 240 && tx >= 0 && tx < Width && ty >= 0 && ty < Height && true)
            {
              int32_t curIdx = (baseSprite + ((ty / 8) * pitch) + ((tx / 8) * scale)) * 32 + ((ty & 7) * 4) + ((tx & 7) / 2);
              int32_t lookup = processor->ReadU8(0x10000 + curIdx, vRamStart);
              if ((tx & 1) == 0)
              {
                lookup &= 0xf;
              }
              else
              {
                lookup >>= 4;
              }
              if (lookup != 0)
              {
          uint16_t pixelColor = processor->ReadU16(palIdx + lookup * 2, palRamStart);
                uint16_t r = (uint8_t)((pixelColor) & 0x1F);       //First 5 Bits
                uint16_t g = (uint8_t)((pixelColor >> 5) & 0x1F);  //Middle 5 Bits
                uint16_t b = (uint8_t)((pixelColor >> 10) & 0x1F);   //Last 5 Bits
                r = r + (((0x1F - r) * blendY) >> 4);
                g = g + (((0x1F - g) * blendY) >> 4);
                b = b + (((0x1F - b) * blendY) >> 4);
                pixelColor = ((uint8_t)(b) << 0) | ((uint8_t)(g) << 5) | ((uint8_t)(r) << 11);
                DrawPixel(curLine, (i & 0x1ff), pixelColor); 
                Blend[(i & 0x1ff)] = blendMaskType;
              }
            }
            rx += dx;
            ry += dy;
          }
        }
      }
    }
  }
}

void GBA::DrawSpritesBrightDec(int32_t priority)
{
  // OBJ must be enabled in this.dispCnt
  if ((dispCnt & (1 << 12)) == 0) return;

  uint8_t blendMaskType = (uint8_t)(1 << 4);

  for (int32_t oamNum = 127; oamNum >= 0; oamNum--)
  {
    uint16_t attr2 = processor->ReadU16Debug(OAM_BASE + (uint32_t)(oamNum * 8) + 4);

    if (((attr2 >> 10) & 3) != priority) continue;

    uint16_t attr0 = processor->ReadU16Debug(OAM_BASE + (uint32_t)(oamNum * 8) + 0);
    uint16_t attr1 = processor->ReadU16Debug(OAM_BASE + (uint32_t)(oamNum * 8) + 2);

    int32_t x = attr1 & 0x1FF;
    int32_t y = attr0 & 0xFF;

    bool semiTransparent = false;

    switch ((attr0 >> 10) & 3)
    {
    case 1:
      // Semi-transparent
      semiTransparent = true;
      break;
    case 2:
      // Obj window
      continue;
    case 3:
      continue;
    }

    if ((dispCnt & 0x7) >= 3 && (attr2 & 0x3FF) < 0x200) continue;

    int32_t Width = -1, Height = -1;
    switch ((attr0 >> 14) & 3)
    {
    case 0:
      // Square
      switch ((attr1 >> 14) & 3)
      {
      case 0: Width = 8; Height = 8; break;
      case 1: Width = 16; Height = 16; break;
      case 2: Width = 32; Height = 32; break;
      case 3: Width = 64; Height = 64; break;
      }
      break;
    case 1:
      // Horizontal Rectangle
      switch ((attr1 >> 14) & 3)
      {
      case 0: Width = 16; Height = 8; break;
      case 1: Width = 32; Height = 8; break;
      case 2: Width = 32; Height = 16; break;
      case 3: Width = 64; Height = 32; break;
      }
      break;
    case 2:
      // Vertical Rectangle
      switch ((attr1 >> 14) & 3)
      {
      case 0: Width = 8; Height = 16; break;
      case 1: Width = 8; Height = 32; break;
      case 2: Width = 16; Height = 32; break;
      case 3: Width = 32; Height = 64; break;
      }
      break;
    }

    // Check double size flag here

    int32_t rWidth = Width, rHeight = Height;
    if ((attr0 & (1 << 8)) != 0)
    {
      // Rot-scale on
      if ((attr0 & (1 << 9)) != 0)
      {
        rWidth *= 2;
        rHeight *= 2;
      }
    }
    else
    {
      // Invalid sprite
      if ((attr0 & (1 << 9)) != 0)
        Width = -1;
    }

    if (Width == -1)
    {
      // Invalid sprite
      continue;
    }

    // Y clipping
    if (y > ((y + rHeight) & 0xff))
    {
      if (curLine >= ((y + rHeight) & 0xff) && !(y < curLine)) continue;
    }
    else
    {
      if (curLine < y || curLine >= ((y + rHeight) & 0xff)) continue;
    }

    int32_t scale = 1;
    if ((attr0 & (1 << 13)) != 0) scale = 2;

    int32_t spritey = curLine - y;
    if (spritey < 0) spritey += 256;

    if (semiTransparent)
    {
      if ((attr0 & (1 << 8)) == 0)
      {
        if ((attr1 & (1 << 13)) != 0) spritey = (Height - 1) - spritey;

        int32_t baseSprite;
        if ((dispCnt & (1 << 6)) != 0)
        {
          // 1 dimensional
          baseSprite = (attr2 & 0x3FF) + ((spritey / 8) * (Width / 8)) * scale;
        }
        else
        {
          // 2 dimensional
          baseSprite = (attr2 & 0x3FF) + ((spritey / 8) * 0x20);
        }

        int32_t baseInc = scale;
        if ((attr1 & (1 << 12)) != 0)
        {
          baseSprite += ((Width / 8) * scale) - scale;
          baseInc = -baseInc;
        }

        if ((attr0 & (1 << 13)) != 0)
        {
          // 256 colors
          for (int32_t i = x; i < x + Width; i++)
          {
            if ((i & 0x1ff) < 240 && true)
            {
              int32_t tx = (i - x) & 7;
              if ((attr1 & (1 << 12)) != 0) tx = 7 - tx;
              int32_t curIdx = baseSprite * 32 + ((spritey & 7) * 8) + tx;
              int32_t lookup = processor->ReadU8(0x10000 + curIdx, vRamStart);
              if (lookup != 0)
              {
                uint16_t pixelColor = processor->ReadU16(0x200 + lookup * 2, palRamStart);
                
                if ((Blend[i & 0x1ff] & blendTarget) != 0 && Blend[i & 0x1ff] != blendMaskType)
                {
                  uint16_t r = (uint8_t)((((pixelColor) & 0x1F) * blendA) >> 4);       //First 5 Bits
                  uint16_t g = (uint8_t)((((pixelColor >> 5) & 0x1F) * blendA) >> 4);  //Middle 5 Bits
                  uint16_t b = (uint8_t)((((pixelColor >> 10) & 0x1F) * blendA) >> 4);   //Last 5 Bits
                  uint16_t sourceValue = tft->dgetPixel(curLine, (i & 0x1ff));
                  r += (uint8_t)((((sourceValue >> 11) & 0x1F) * blendB) >> 4); //R
                  g += (uint8_t)((((sourceValue >> 5) & 0x3F) * blendB) >> 4); //G
                  b += (uint8_t)((((sourceValue) & 0x1F) * blendB) >> 4); //B
                  if (r > 0xff) r = 0xff;
                  if (g > 0xff) g = 0xff;
                  if (b > 0xff) b = 0xff;
                  pixelColor = ((uint8_t)(b) << 0) | ((uint8_t)(g) << 5) | ((uint8_t)(r) << 11);
                }
                else
                {
                  pixelColor = GBAToColor(pixelColor);
                }
                
                DrawPixel(curLine, (i & 0x1ff), pixelColor); 
                Blend[(i & 0x1ff)] = blendMaskType;
              }
            }
            if (((i - x) & 7) == 7) baseSprite += baseInc;
          }
        }
        else
        {
          // 16 colors
          int32_t palIdx = 0x200 + (((attr2 >> 12) & 0xF) * 16 * 2);
          for (int32_t i = x; i < x + Width; i++)
          {
            if ((i & 0x1ff) < 240 && true)
            {
              int32_t tx = (i - x) & 7;
              if ((attr1 & (1 << 12)) != 0) tx = 7 - tx;
              int32_t curIdx = baseSprite * 32 + ((spritey & 7) * 4) + (tx / 2);
              int32_t lookup = processor->ReadU8(0x10000 + curIdx, vRamStart);
              if ((tx & 1) == 0)
              {
                lookup &= 0xf;
              }
              else
              {
                lookup >>= 4;
              }
              if (lookup != 0)
              {
                uint16_t pixelColor = processor->ReadU16(palIdx + lookup * 2, palRamStart);
                
                if ((Blend[i & 0x1ff] & blendTarget) != 0 && Blend[i & 0x1ff] != blendMaskType)
                {
                  uint16_t r = (uint8_t)((((pixelColor) & 0x1F) * blendA) >> 4);       //First 5 Bits
                  uint16_t g = (uint8_t)((((pixelColor >> 5) & 0x1F) * blendA) >> 4);  //Middle 5 Bits
                  uint16_t b = (uint8_t)((((pixelColor >> 10) & 0x1F) * blendA) >> 4);   //Last 5 Bits
                  uint16_t sourceValue = tft->dgetPixel(curLine, (i & 0x1ff));
                  r += (uint8_t)((((sourceValue >> 11) & 0x1F) * blendB) >> 4); //R
                  g += (uint8_t)((((sourceValue >> 5) & 0x3F) * blendB) >> 4); //G
                  b += (uint8_t)((((sourceValue) & 0x1F) * blendB) >> 4); //B
                  if (r > 0xff) r = 0xff;
                  if (g > 0xff) g = 0xff;
                  if (b > 0xff) b = 0xff;
                  pixelColor = ((uint8_t)(b) << 0) | ((uint8_t)(g) << 5) | ((uint8_t)(r) << 11);
                }
                else
                {
                  pixelColor = GBAToColor(pixelColor);
                }
                
                DrawPixel(curLine, (i & 0x1ff), pixelColor); 
                Blend[(i & 0x1ff)] = blendMaskType;
              }
            }
            if (((i - x) & 7) == 7) baseSprite += baseInc;
          }
        }
      }
      else
      {
        int32_t rotScaleParam = (attr1 >> 9) & 0x1F;

        int16_t dx = (int16_t)processor->ReadU16Debug(OAM_BASE + (uint32_t)(rotScaleParam * 8 * 4) + 0x6);
        int16_t dmx = (int16_t)processor->ReadU16Debug(OAM_BASE + (uint32_t)(rotScaleParam * 8 * 4) + 0xE);
        int16_t dy = (int16_t)processor->ReadU16Debug(OAM_BASE + (uint32_t)(rotScaleParam * 8 * 4) + 0x16);
        int16_t dmy = (int16_t)processor->ReadU16Debug(OAM_BASE + (uint32_t)(rotScaleParam * 8 * 4) + 0x1E);

        int32_t cx = rWidth / 2;
        int32_t cy = rHeight / 2;

        int32_t baseSprite = attr2 & 0x3FF;
        int32_t pitch;

        if ((dispCnt & (1 << 6)) != 0)
        {
          // 1 dimensional
          pitch = (Width / 8) * scale;
        }
        else
        {
          // 2 dimensional
          pitch = 0x20;
        }

        int32_t rx = (int32_t)((dmx * (spritey - cy)) - (cx * dx) + (Width << 7));
        int32_t ry = (int32_t)((dmy * (spritey - cy)) - (cx * dy) + (Height << 7));

        // Draw a rot/scale sprite
        if ((attr0 & (1 << 13)) != 0)
        {
          // 256 colors
          for (int32_t i = x; i < x + rWidth; i++)
          {
            int32_t tx = rx >> 8;
            int32_t ty = ry >> 8;

            if ((i & 0x1ff) < 240 && tx >= 0 && tx < Width && ty >= 0 && ty < Height && true)
            {
              int32_t curIdx = (baseSprite + ((ty / 8) * pitch) + ((tx / 8) * scale)) * 32 + ((ty & 7) * 8) + (tx & 7);
              int32_t lookup = processor->ReadU8(0x10000 + curIdx, vRamStart);
              if (lookup != 0)
              {
                uint16_t pixelColor = processor->ReadU16(0x200 + lookup * 2, palRamStart);
                
                if ((Blend[i & 0x1ff] & blendTarget) != 0 && Blend[i & 0x1ff] != blendMaskType)
                {
                  uint16_t r = (uint8_t)((((pixelColor) & 0x1F) * blendA) >> 4);       //First 5 Bits
                  uint16_t g = (uint8_t)((((pixelColor >> 5) & 0x1F) * blendA) >> 4);  //Middle 5 Bits
                  uint16_t b = (uint8_t)((((pixelColor >> 10) & 0x1F) * blendA) >> 4);   //Last 5 Bits
                  uint16_t sourceValue = tft->dgetPixel(curLine, (i & 0x1ff));
                  r += (uint8_t)((((sourceValue >> 11) & 0x1F) * blendB) >> 4); //R
                  g += (uint8_t)((((sourceValue >> 5) & 0x3F) * blendB) >> 4); //G
                  b += (uint8_t)((((sourceValue) & 0x1F) * blendB) >> 4); //B
                  if (r > 0xff) r = 0xff;
                  if (g > 0xff) g = 0xff;
                  if (b > 0xff) b = 0xff;
                  pixelColor = ((uint8_t)(b) << 0) | ((uint8_t)(g) << 5) | ((uint8_t)(r) << 11);
                }
                else
                {
                  pixelColor = GBAToColor(pixelColor);
                }
                
                DrawPixel(curLine, (i & 0x1ff), pixelColor); 
                Blend[(i & 0x1ff)] = blendMaskType;
              }
            }
            rx += dx;
            ry += dy;
          }
        }
        else
        {
          // 16 colors
          int32_t palIdx = 0x200 + (((attr2 >> 12) & 0xF) * 16 * 2);
          for (int32_t i = x; i < x + rWidth; i++)
          {
            int32_t tx = rx >> 8;
            int32_t ty = ry >> 8;

            if ((i & 0x1ff) < 240 && tx >= 0 && tx < Width && ty >= 0 && ty < Height && true)
            {
              int32_t curIdx = (baseSprite + ((ty / 8) * pitch) + ((tx / 8) * scale)) * 32 + ((ty & 7) * 4) + ((tx & 7) / 2);
              int32_t lookup = processor->ReadU8(0x10000 + curIdx, vRamStart);
              if ((tx & 1) == 0)
              {
                lookup &= 0xf;
              }
              else
              {
                lookup >>= 4;
              }
              if (lookup != 0)
              {
                uint16_t pixelColor = processor->ReadU16(palIdx + lookup * 2, palRamStart);
                
                if ((Blend[i & 0x1ff] & blendTarget) != 0 && Blend[i & 0x1ff] != blendMaskType)
                {
                  uint16_t r = (uint8_t)((((pixelColor) & 0x1F) * blendA) >> 4);       //First 5 Bits
                  uint16_t g = (uint8_t)((((pixelColor >> 5) & 0x1F) * blendA) >> 4);  //Middle 5 Bits
                  uint16_t b = (uint8_t)((((pixelColor >> 10) & 0x1F) * blendA) >> 4);   //Last 5 Bits
                  uint16_t sourceValue = tft->dgetPixel(curLine, (i & 0x1ff));
                  r += (uint8_t)((((sourceValue >> 11) & 0x1F) * blendB) >> 4); //R
                  g += (uint8_t)((((sourceValue >> 5) & 0x3F) * blendB) >> 4); //G
                  b += (uint8_t)((((sourceValue) & 0x1F) * blendB) >> 4); //B
                  if (r > 0xff) r = 0xff;
                  if (g > 0xff) g = 0xff;
                  if (b > 0xff) b = 0xff;
                  pixelColor = ((uint8_t)(b) << 0) | ((uint8_t)(g) << 5) | ((uint8_t)(r) << 11);
                }
                else
                {
                  pixelColor = GBAToColor(pixelColor);
                }
                
                DrawPixel(curLine, (i & 0x1ff), pixelColor); 
                Blend[(i & 0x1ff)] = blendMaskType;
              }
            }
            rx += dx;
            ry += dy;
          }
        }
      }
    }
    else
    {
      if ((attr0 & (1 << 8)) == 0)
      {
        if ((attr1 & (1 << 13)) != 0) spritey = (Height - 1) - spritey;

        int32_t baseSprite;
        if ((dispCnt & (1 << 6)) != 0)
        {
          // 1 dimensional
          baseSprite = (attr2 & 0x3FF) + ((spritey / 8) * (Width / 8)) * scale;
        }
        else
        {
          // 2 dimensional
          baseSprite = (attr2 & 0x3FF) + ((spritey / 8) * 0x20);
        }

        int32_t baseInc = scale;
        if ((attr1 & (1 << 12)) != 0)
        {
          baseSprite += ((Width / 8) * scale) - scale;
          baseInc = -baseInc;
        }

        if ((attr0 & (1 << 13)) != 0)
        {
          // 256 colors
          for (int32_t i = x; i < x + Width; i++)
          {
            if ((i & 0x1ff) < 240 && true)
            {
              int32_t tx = (i - x) & 7;
              if ((attr1 & (1 << 12)) != 0) tx = 7 - tx;
              int32_t curIdx = baseSprite * 32 + ((spritey & 7) * 8) + tx;
              int32_t lookup = processor->ReadU8(0x10000 + curIdx, vRamStart);
              if (lookup != 0)
              {
                uint16_t pixelColor = processor->ReadU16(0x200 + lookup * 2, palRamStart);
                uint16_t r = (uint8_t)((pixelColor) & 0x1F);      //First 5 Bits
                uint16_t g = (uint8_t)((pixelColor >> 5) & 0x1F);  //Middle 5 Bits
                uint16_t b = (uint8_t)((pixelColor >> 10) & 0x1F);   //Last 5 Bits 
                r = r - ((r * blendY) >> 4);
                g = g - ((g * blendY) >> 4);
                b = b - ((b * blendY) >> 4);
                pixelColor = ((uint8_t)(b) << 0) | ((uint8_t)(g) << 5) | ((uint8_t)(r) << 11);
                DrawPixel(curLine, (i & 0x1ff), pixelColor); 
                Blend[(i & 0x1ff)] = blendMaskType;
              }
            }
            if (((i - x) & 7) == 7) baseSprite += baseInc;
          }
        }
        else
        {
          // 16 colors
          int32_t palIdx = 0x200 + (((attr2 >> 12) & 0xF) * 16 * 2);
          for (int32_t i = x; i < x + Width; i++)
          {
            if ((i & 0x1ff) < 240 && true)
            {
              int32_t tx = (i - x) & 7;
              if ((attr1 & (1 << 12)) != 0) tx = 7 - tx;
              int32_t curIdx = baseSprite * 32 + ((spritey & 7) * 4) + (tx / 2);
              int32_t lookup = processor->ReadU8(0x10000 + curIdx, vRamStart);
              if ((tx & 1) == 0)
              {
                lookup &= 0xf;
              }
              else
              {
                lookup >>= 4;
              }
              if (lookup != 0)
              {
                uint16_t pixelColor = processor->ReadU16(palIdx + lookup * 2, palRamStart);
                uint16_t r = (uint8_t)((pixelColor) & 0x1F);      //First 5 Bits
                uint16_t g = (uint8_t)((pixelColor >> 5) & 0x1F);  //Middle 5 Bits
                uint16_t b = (uint8_t)((pixelColor >> 10) & 0x1F);   //Last 5 Bits 
                r = r - ((r * blendY) >> 4);
                g = g - ((g * blendY) >> 4);
                b = b - ((b * blendY) >> 4);
                pixelColor = ((uint8_t)(b) << 0) | ((uint8_t)(g) << 5) | ((uint8_t)(r) << 11);
                DrawPixel(curLine, (i & 0x1ff), pixelColor); 
                Blend[(i & 0x1ff)] = blendMaskType;
              }
            }
            if (((i - x) & 7) == 7) baseSprite += baseInc;
          }
        }
      }
      else
      {
        int32_t rotScaleParam = (attr1 >> 9) & 0x1F;

        int16_t dx = (int16_t)processor->ReadU16Debug(OAM_BASE + (uint32_t)(rotScaleParam * 8 * 4) + 0x6);
        int16_t dmx = (int16_t)processor->ReadU16Debug(OAM_BASE + (uint32_t)(rotScaleParam * 8 * 4) + 0xE);
        int16_t dy = (int16_t)processor->ReadU16Debug(OAM_BASE + (uint32_t)(rotScaleParam * 8 * 4) + 0x16);
        int16_t dmy = (int16_t)processor->ReadU16Debug(OAM_BASE + (uint32_t)(rotScaleParam * 8 * 4) + 0x1E);

        int32_t cx = rWidth / 2;
        int32_t cy = rHeight / 2;

        int32_t baseSprite = attr2 & 0x3FF;
        int32_t pitch;

        if ((dispCnt & (1 << 6)) != 0)
        {
          // 1 dimensional
          pitch = (Width / 8) * scale;
        }
        else
        {
          // 2 dimensional
          pitch = 0x20;
        }

        int32_t rx = (int32_t)((dmx * (spritey - cy)) - (cx * dx) + (Width << 7));
        int32_t ry = (int32_t)((dmy * (spritey - cy)) - (cx * dy) + (Height << 7));

        // Draw a rot/scale sprite
        if ((attr0 & (1 << 13)) != 0)
        {
          // 256 colors
          for (int32_t i = x; i < x + rWidth; i++)
          {
            int32_t tx = rx >> 8;
            int32_t ty = ry >> 8;

            if ((i & 0x1ff) < 240 && tx >= 0 && tx < Width && ty >= 0 && ty < Height && true)
            {
              int32_t curIdx = (baseSprite + ((ty / 8) * pitch) + ((tx / 8) * scale)) * 32 + ((ty & 7) * 8) + (tx & 7);
              int32_t lookup = processor->ReadU8(0x10000 + curIdx, vRamStart);
              if (lookup != 0)
              {
                uint16_t pixelColor = processor->ReadU16(0x200 + lookup * 2, palRamStart);
                uint16_t r = (uint8_t)((pixelColor) & 0x1F);      //First 5 Bits
                uint16_t g = (uint8_t)((pixelColor >> 5) & 0x1F);  //Middle 5 Bits
                uint16_t b = (uint8_t)((pixelColor >> 10) & 0x1F);   //Last 5 Bits 
                r = r - ((r * blendY) >> 4);
                g = g - ((g * blendY) >> 4);
                b = b - ((b * blendY) >> 4);
                pixelColor = ((uint8_t)(b) << 0) | ((uint8_t)(g) << 5) | ((uint8_t)(r) << 11);
                DrawPixel(curLine, (i & 0x1ff), pixelColor); 
                Blend[(i & 0x1ff)] = blendMaskType;
              }
            }
            rx += dx;
            ry += dy;
          }
        }
        else
        {
          // 16 colors
          int32_t palIdx = 0x200 + (((attr2 >> 12) & 0xF) * 16 * 2);
          for (int i = x; i < x + rWidth; i++)
          {
            int32_t tx = rx >> 8;
            int32_t ty = ry >> 8;

            if ((i & 0x1ff) < 240 && tx >= 0 && tx < Width && ty >= 0 && ty < Height && true)
            {
              int32_t curIdx = (baseSprite + ((ty / 8) * pitch) + ((tx / 8) * scale)) * 32 + ((ty & 7) * 4) + ((tx & 7) / 2);
              int32_t lookup = processor->ReadU8(0x10000 + curIdx, vRamStart);
              if ((tx & 1) == 0)
              {
                lookup &= 0xf;
              }
              else
              {
                lookup >>= 4;
              }
              if (lookup != 0)
              {
                uint16_t pixelColor = processor->ReadU16(palIdx + lookup * 2, palRamStart);
                uint16_t r = (uint8_t)((pixelColor) & 0x1F);      //First 5 Bits
                uint16_t g = (uint8_t)((pixelColor >> 5) & 0x1F);  //Middle 5 Bits
                uint16_t b = (uint8_t)((pixelColor >> 10) & 0x1F);   //Last 5 Bits 
                r = r - ((r * blendY) >> 4);
                g = g - ((g * blendY) >> 4);
                b = b - ((b * blendY) >> 4);
                pixelColor = ((uint8_t)(b) << 0) | ((uint8_t)(g) << 5) | ((uint8_t)(r) << 11);
                DrawPixel(curLine, (i & 0x1ff), pixelColor); 
                Blend[(i & 0x1ff)] = blendMaskType;
              }
            }
            rx += dx;
            ry += dy;
          }
        }
      }
    }
  }
}
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
